robinandreeklund-collab/Strilas/docs/phase1-mounting.png

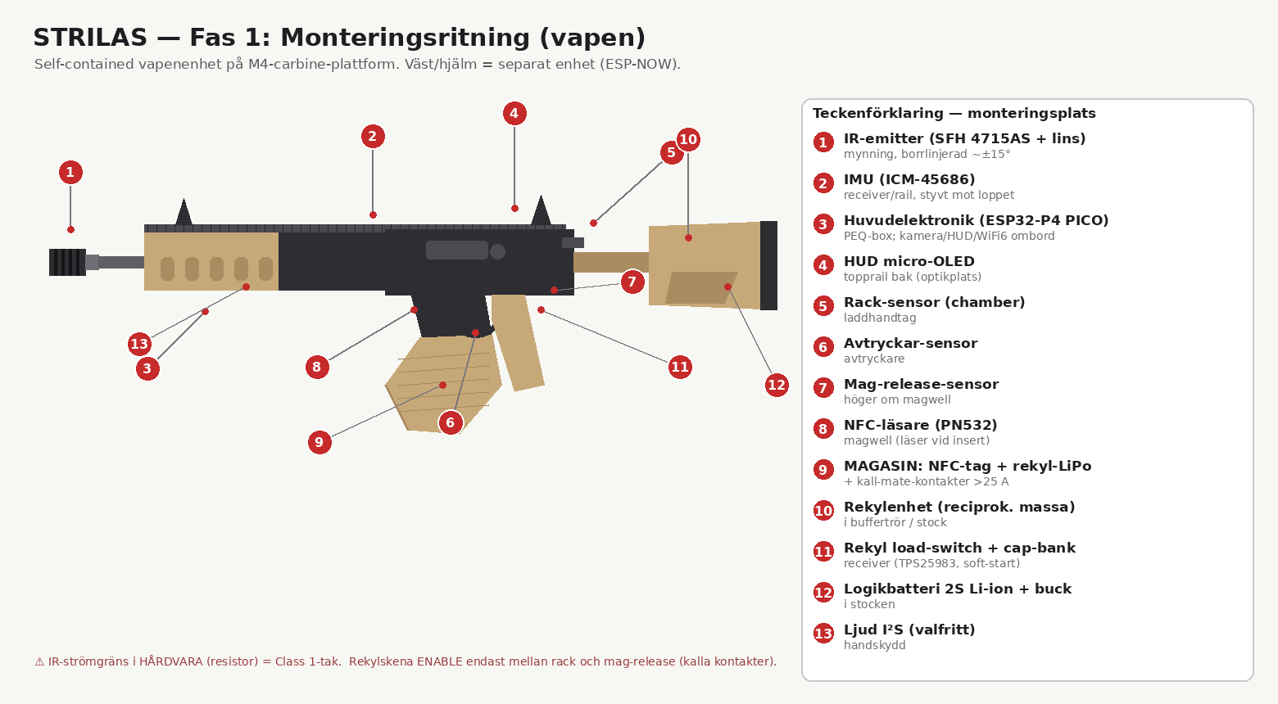
docs/phase1-mounting.png
