robinandreeklund-collab/Strilas/hardware/firecontrol-placement.png

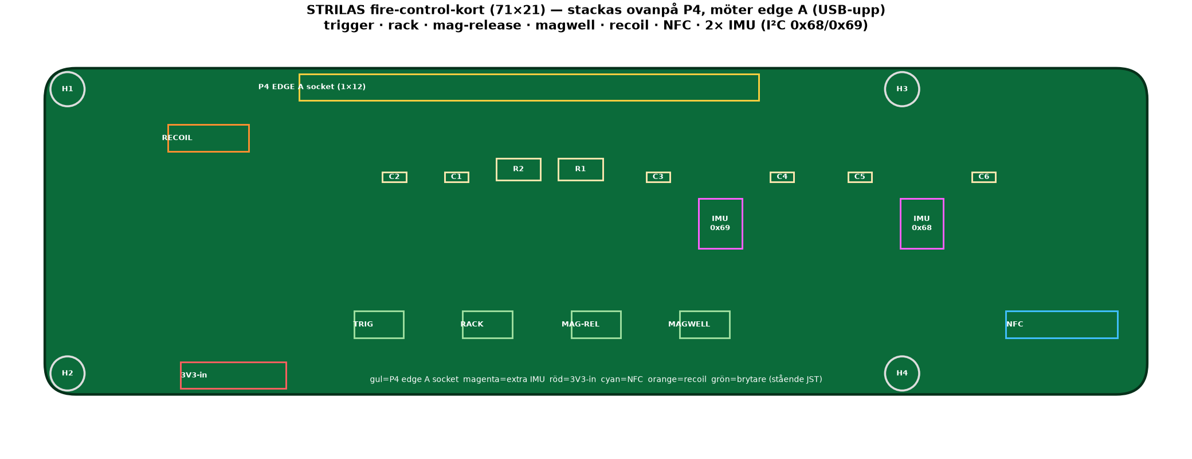
hardware/firecontrol-placement.png
