robinandreeklund-collab/Strilas/vapen-stack/ritningar/ballistik-avstand.png

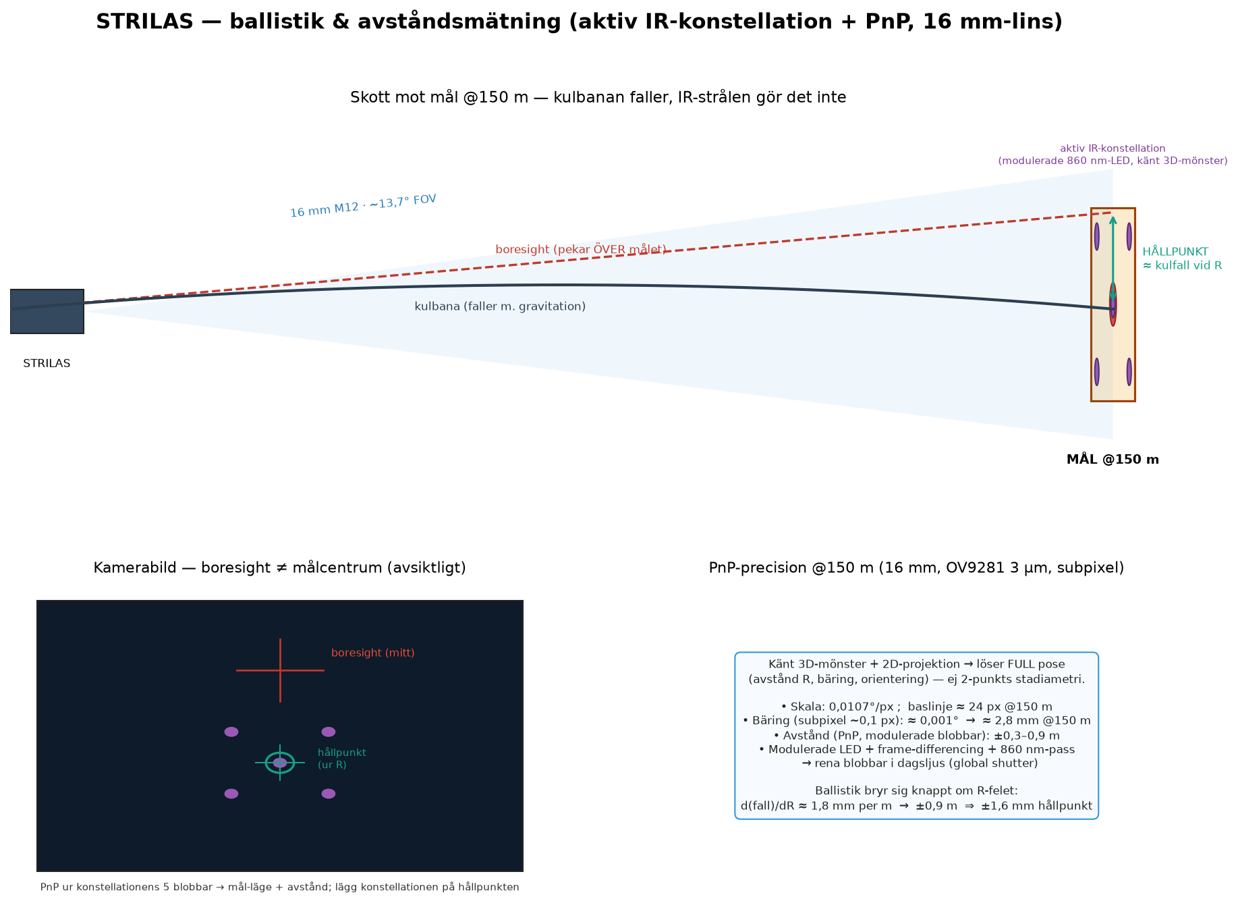
vapen-stack/ritningar/ballistik-avstand.png
