robinandreeklund-collab/Strilas/vapen-stack/ritningar/hitbox-simulering.png

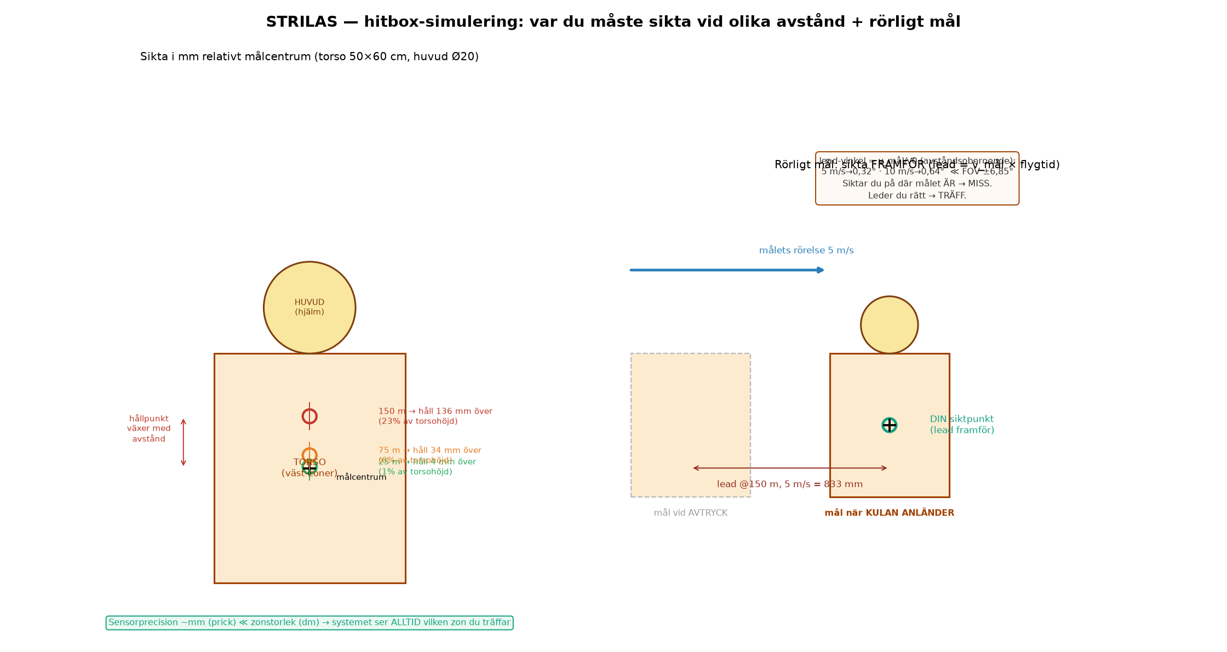
vapen-stack/ritningar/hitbox-simulering.png
