robinandreeklund-collab/Strilas/vapen-stack/ritningar/imu-breakout-koppling.png

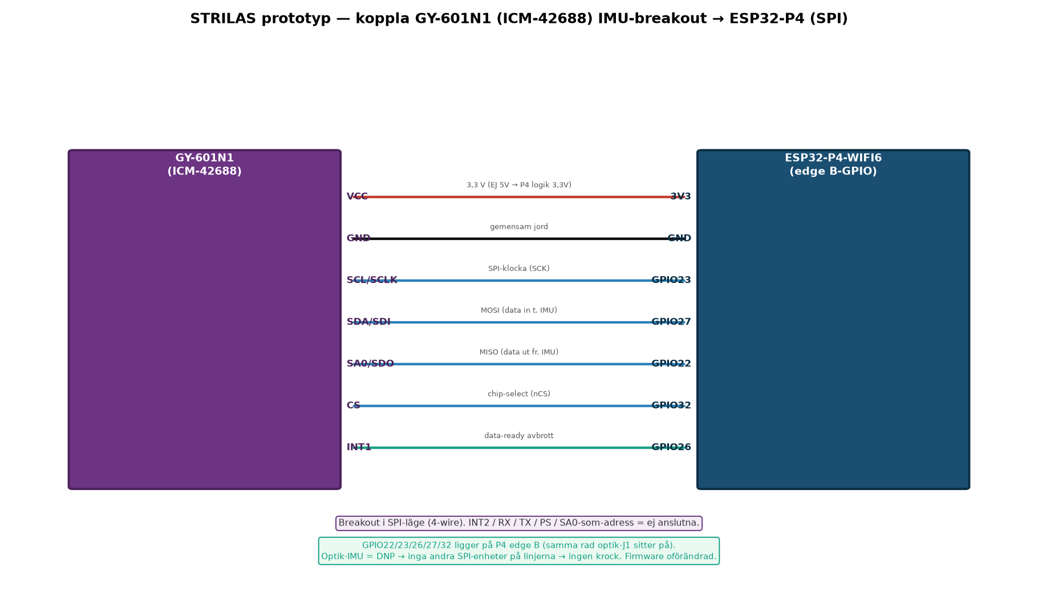
vapen-stack/ritningar/imu-breakout-koppling.png
