robinandreeklund-collab/Strilas/vapen-stack/ritningar/lead-rorligt-mal.png

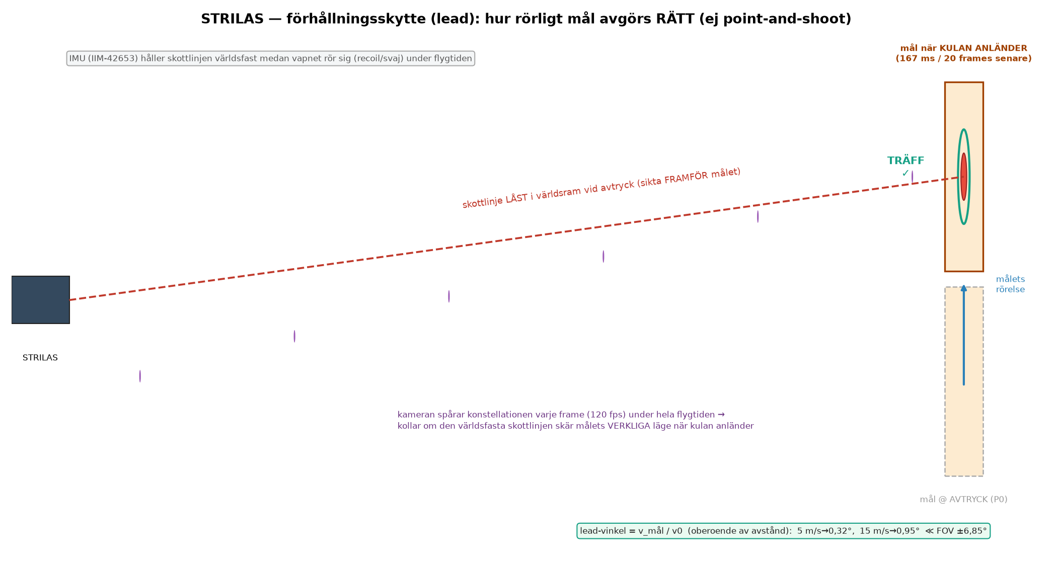
vapen-stack/ritningar/lead-rorligt-mal.png
