robinandreeklund-collab/Strilas/vapen-stack/ritningar/p4-pinmap-fysisk.png

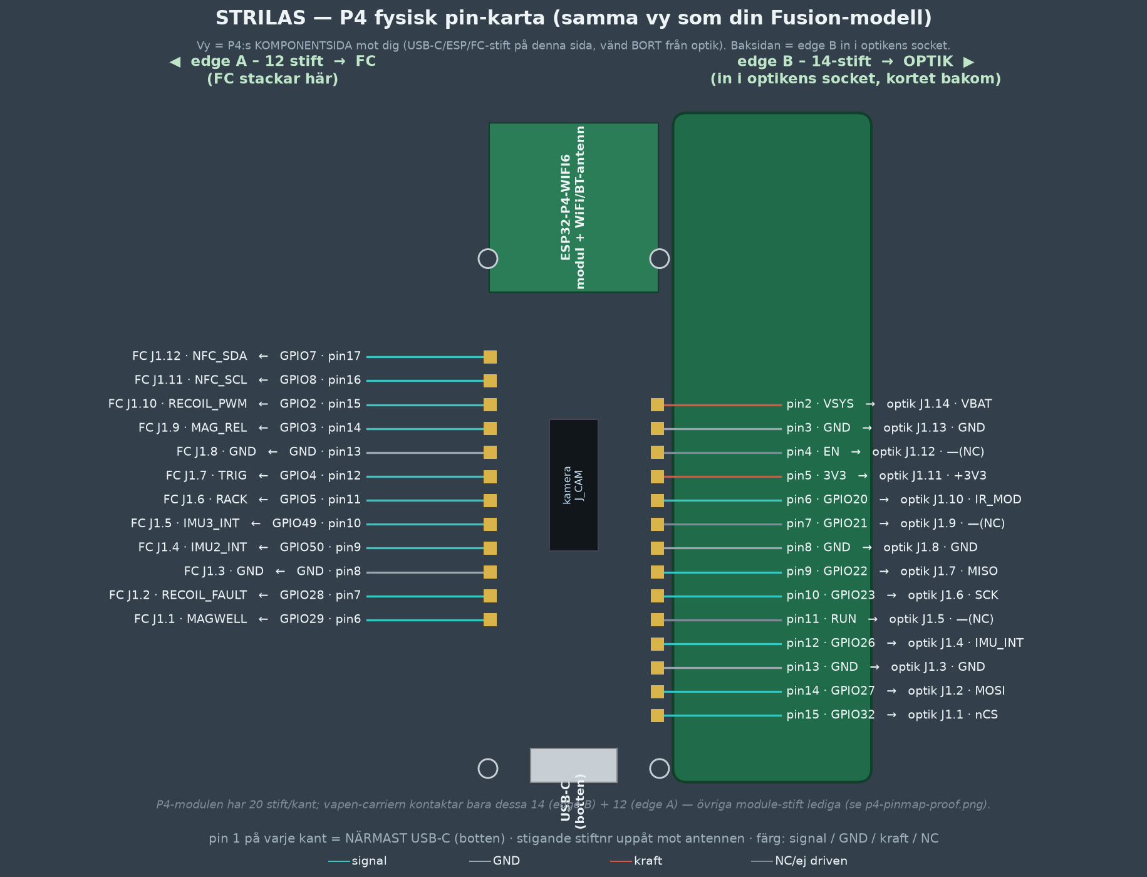
vapen-stack/ritningar/p4-pinmap-fysisk.png
