robinandreeklund-collab/Strilas/vapen-stack/ritningar/p4-pinmap-proof.png

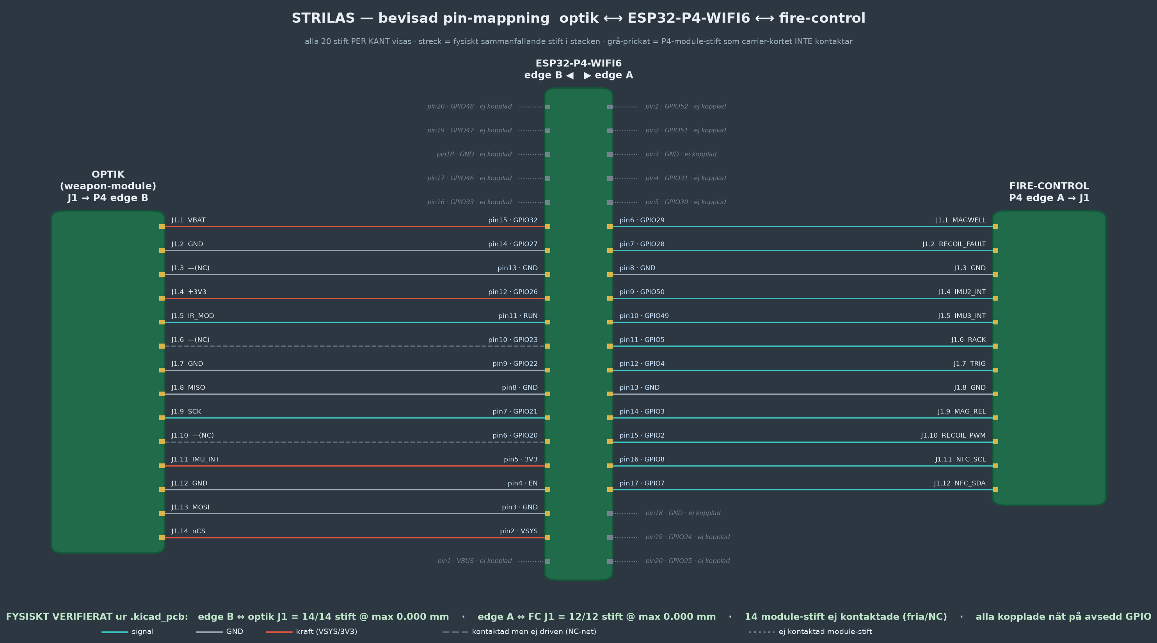
vapen-stack/ritningar/p4-pinmap-proof.png
