robinandreeklund-collab/Strilas/vapen-stack/ritningar/precision-felbudget.png

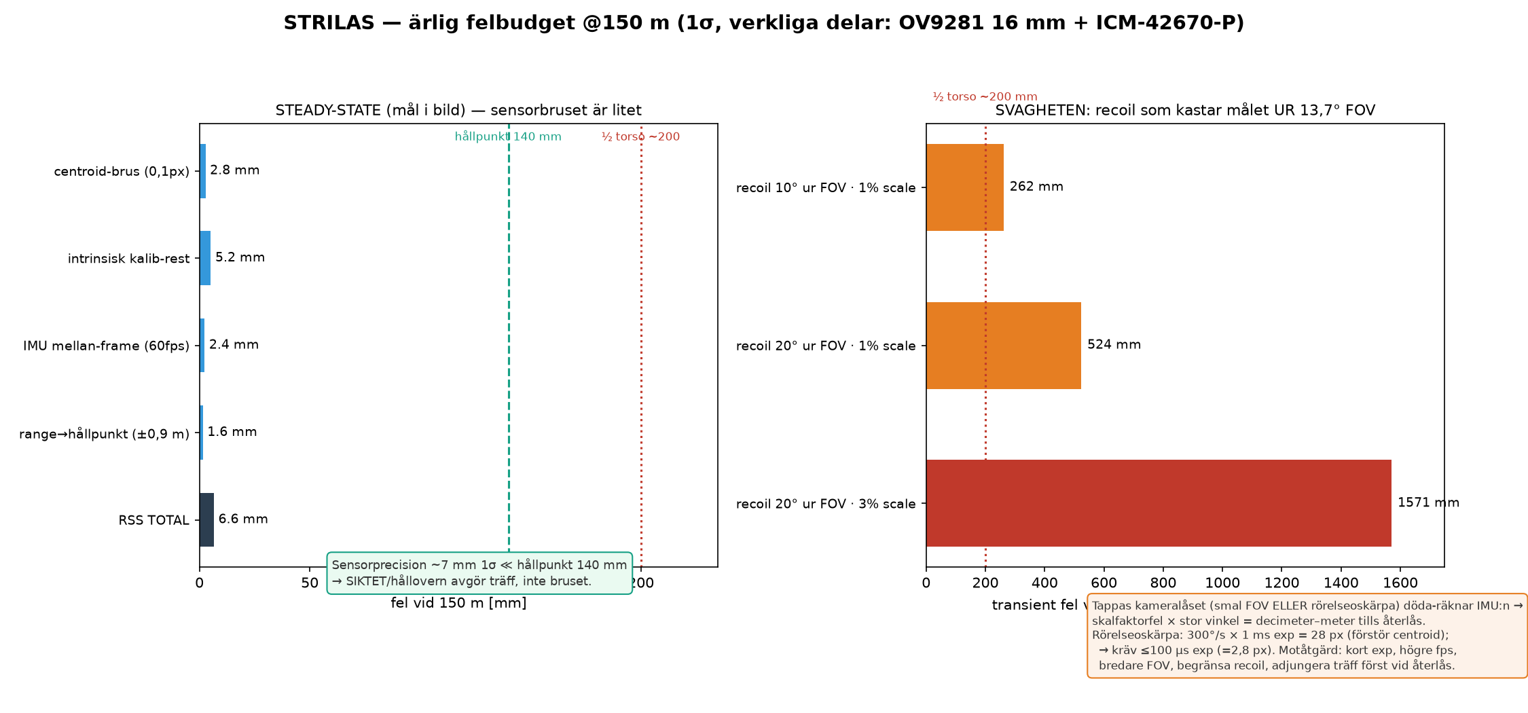
vapen-stack/ritningar/precision-felbudget.png
