robinandreeklund-collab/Strilas/vapen-stack/ritningar/precision-iim42653.png

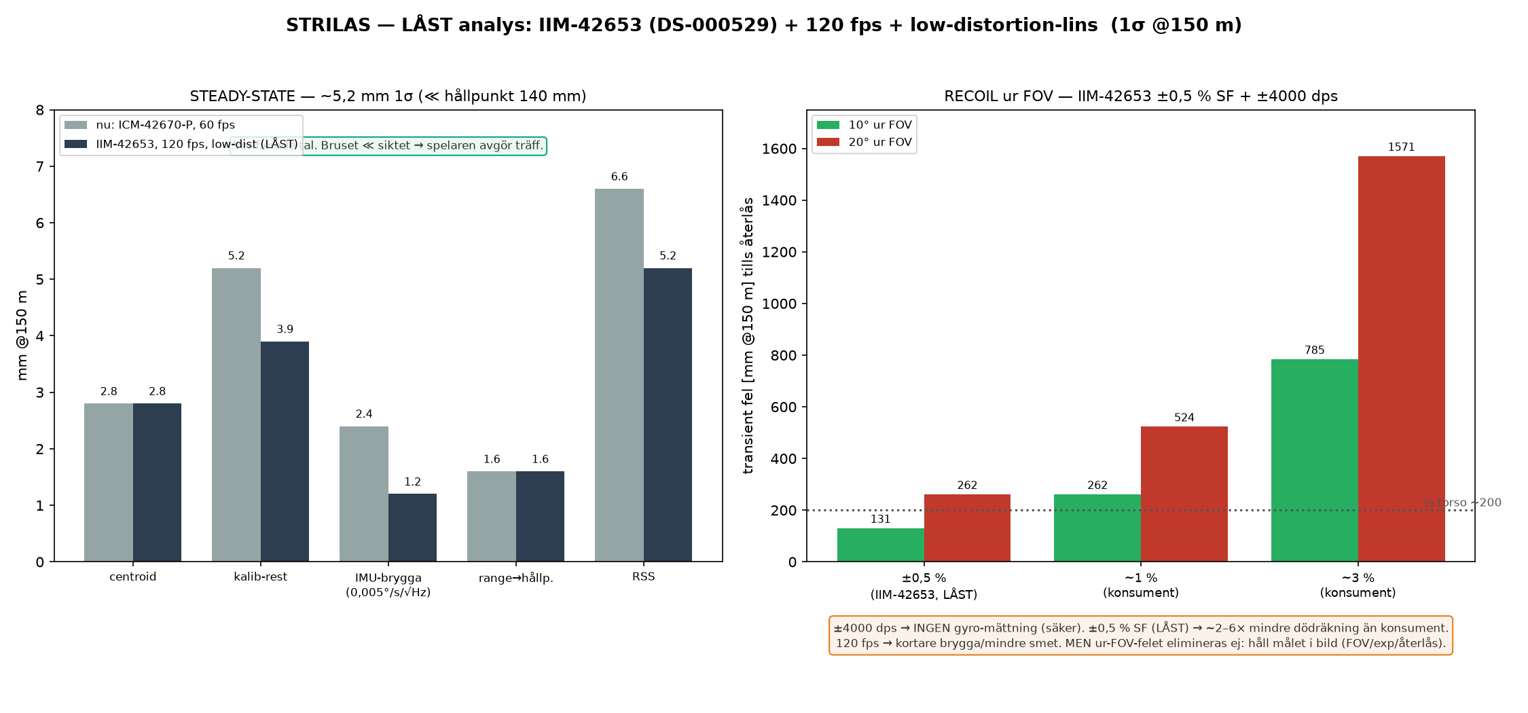
vapen-stack/ritningar/precision-iim42653.png
