robinandreeklund-collab/Strilas/vapen-stack/ritningar/skott-flode.png

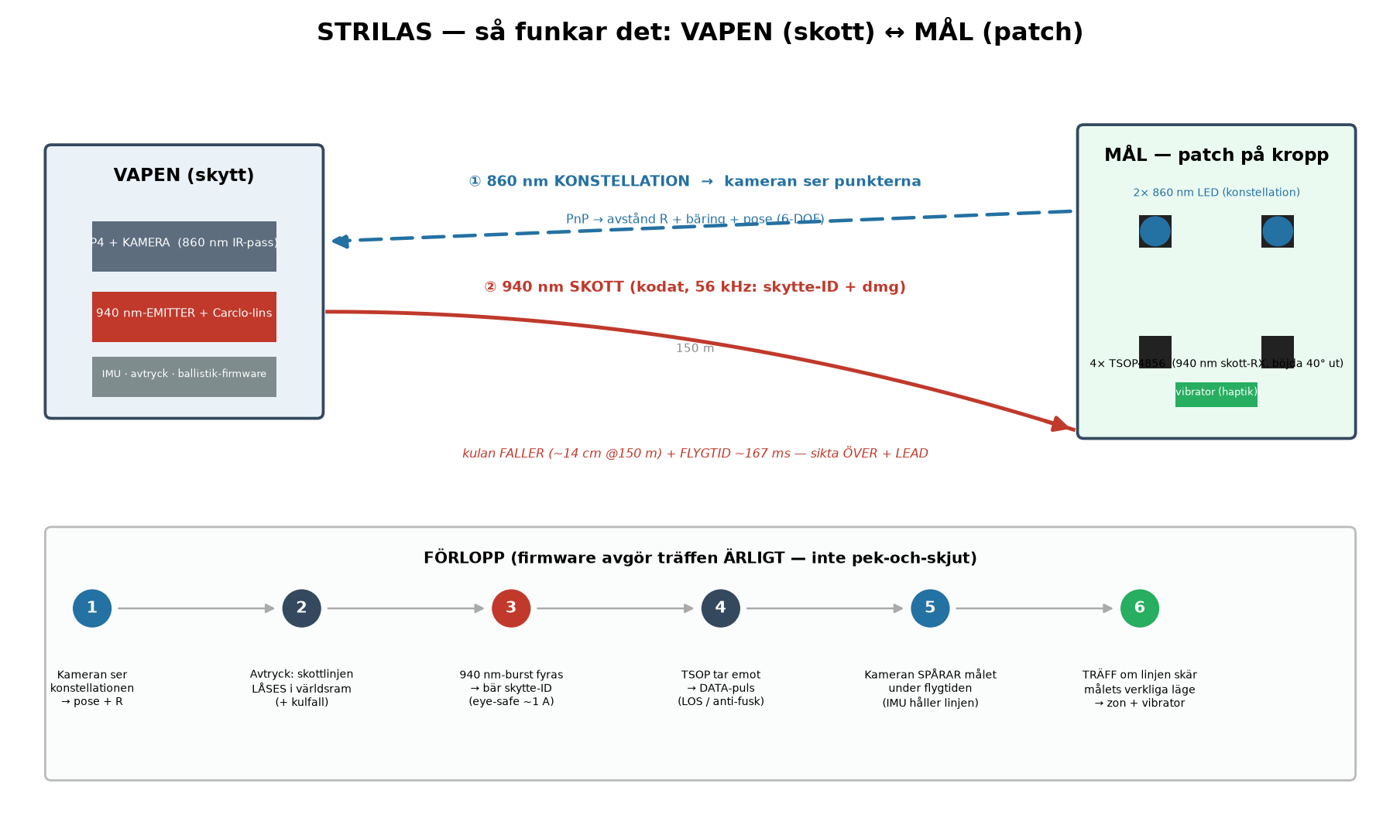
vapen-stack/ritningar/skott-flode.png
