robinandreeklund-collab/Strilas/vapen-stack/ritningar/spelare-topologi.png

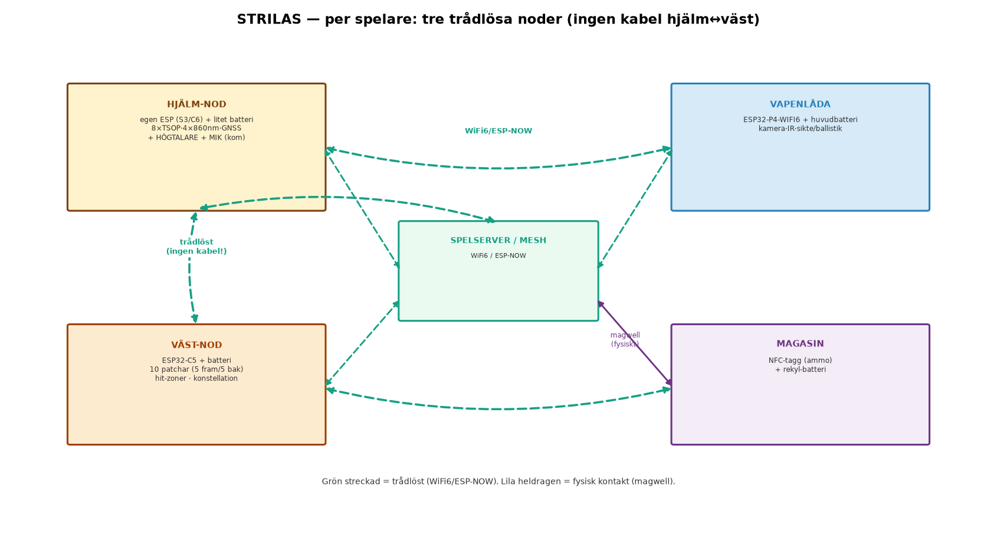
vapen-stack/ritningar/spelare-topologi.png
