robinandreeklund-collab/Strilas/vapen-stack/ritningar/system-helhet.png

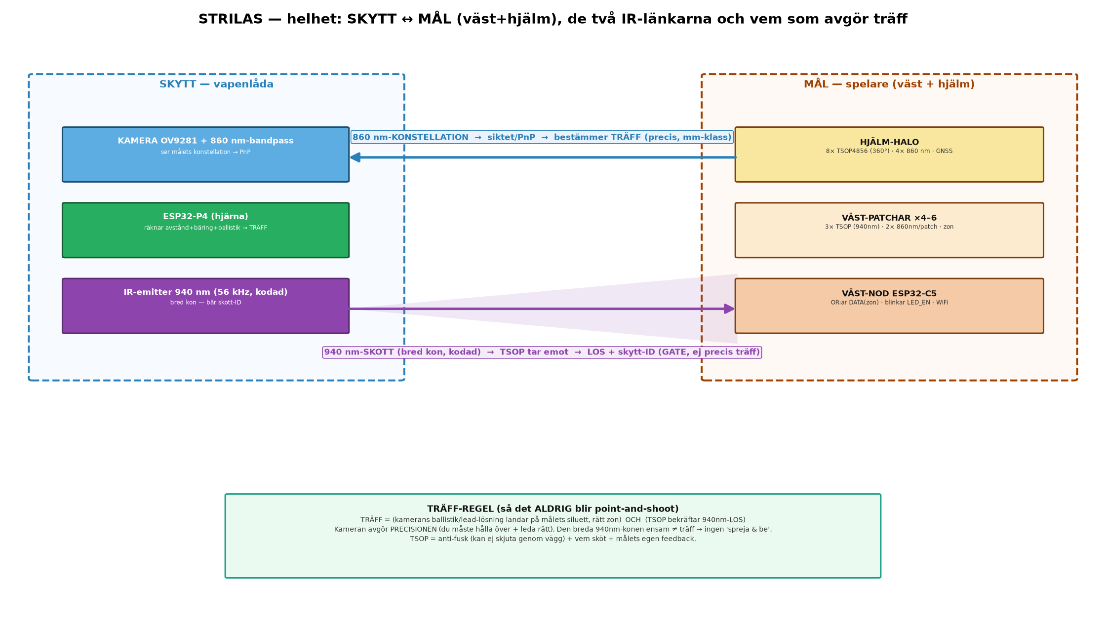
vapen-stack/ritningar/system-helhet.png
