robinandreeklund-collab/Strilas/vapen-stack/ritningar/system-oversikt.png

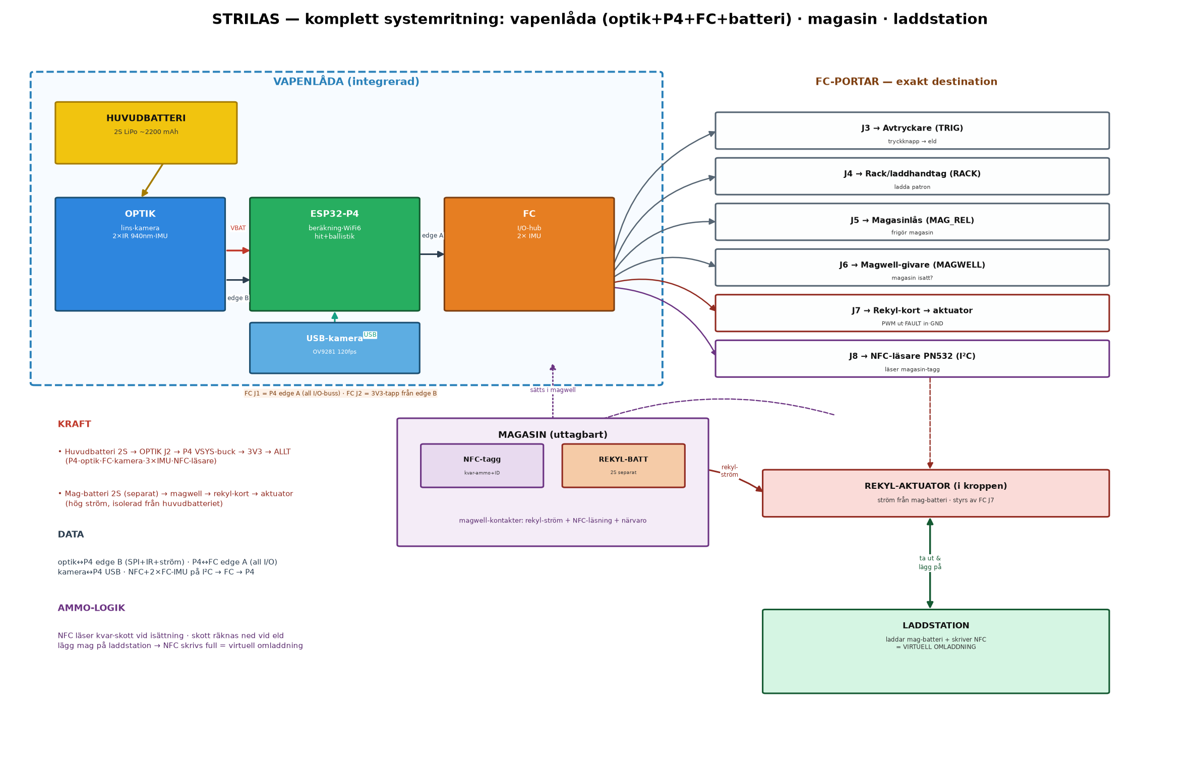
vapen-stack/ritningar/system-oversikt.png
