robinandreeklund-collab/Strilas/vapen-stack/ritningar/vapen-layout.png

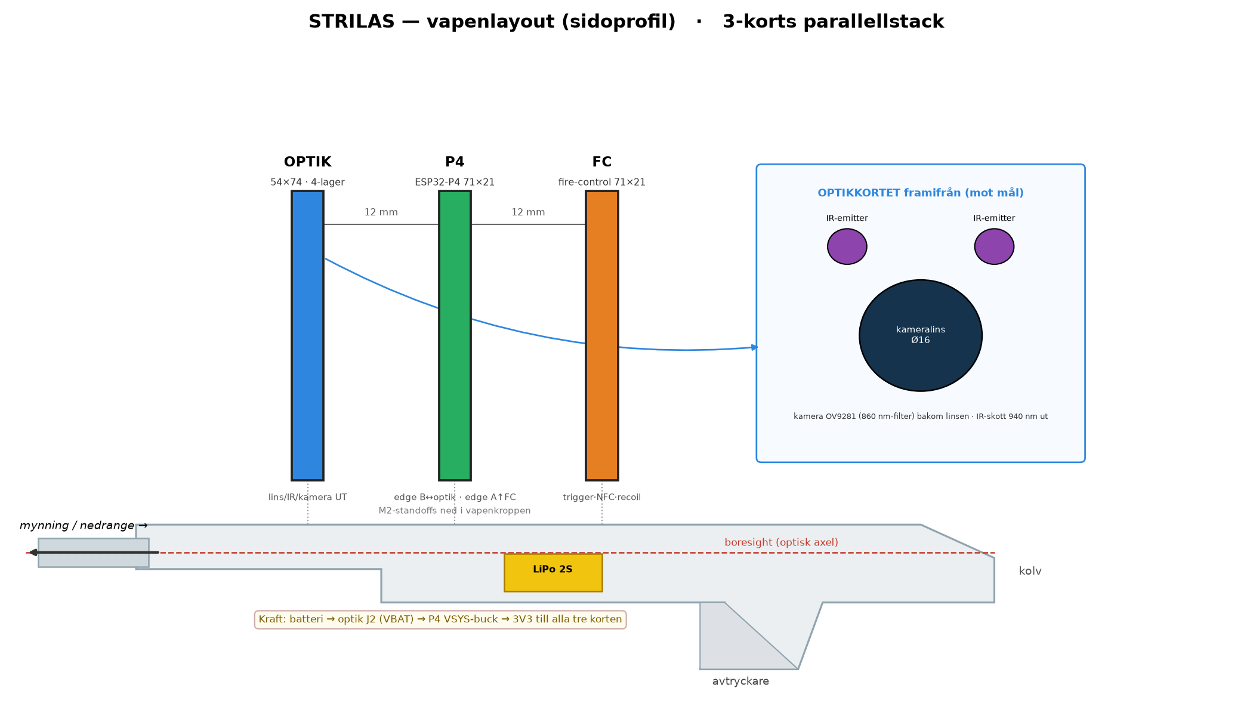
vapen-stack/ritningar/vapen-layout.png
