robinandreeklund-collab/Strilas/vapen-stack/ritningar/vest-haptik.png

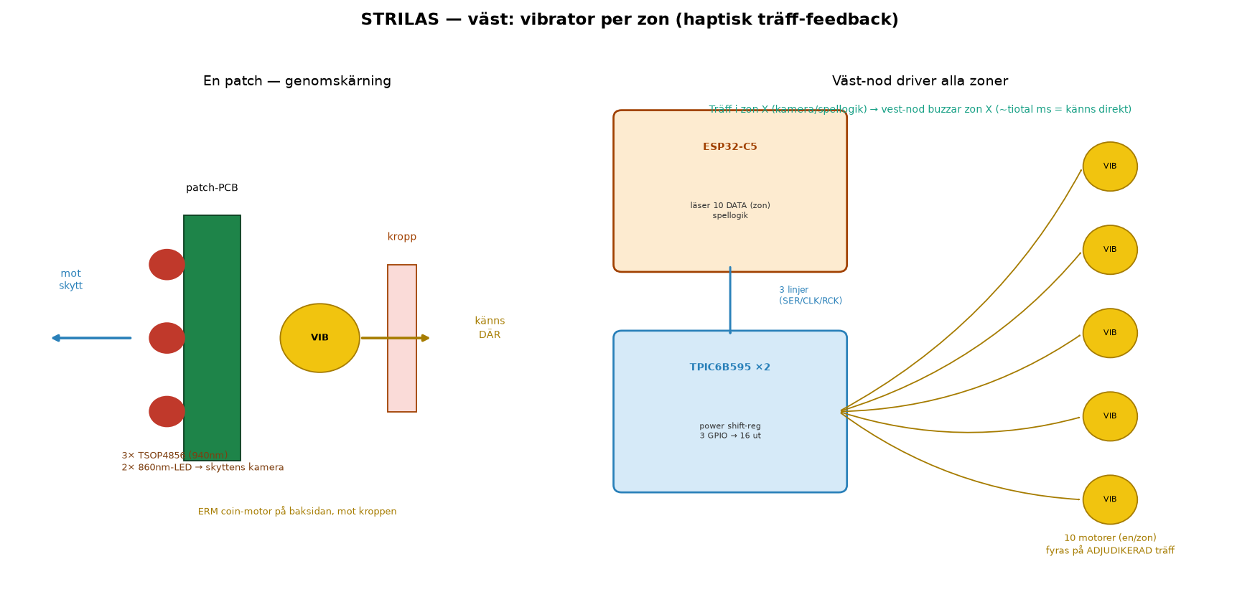
vapen-stack/ritningar/vest-haptik.png
