robinandreeklund-collab/Strilas/vapen-stack/ritningar/zonschema.png

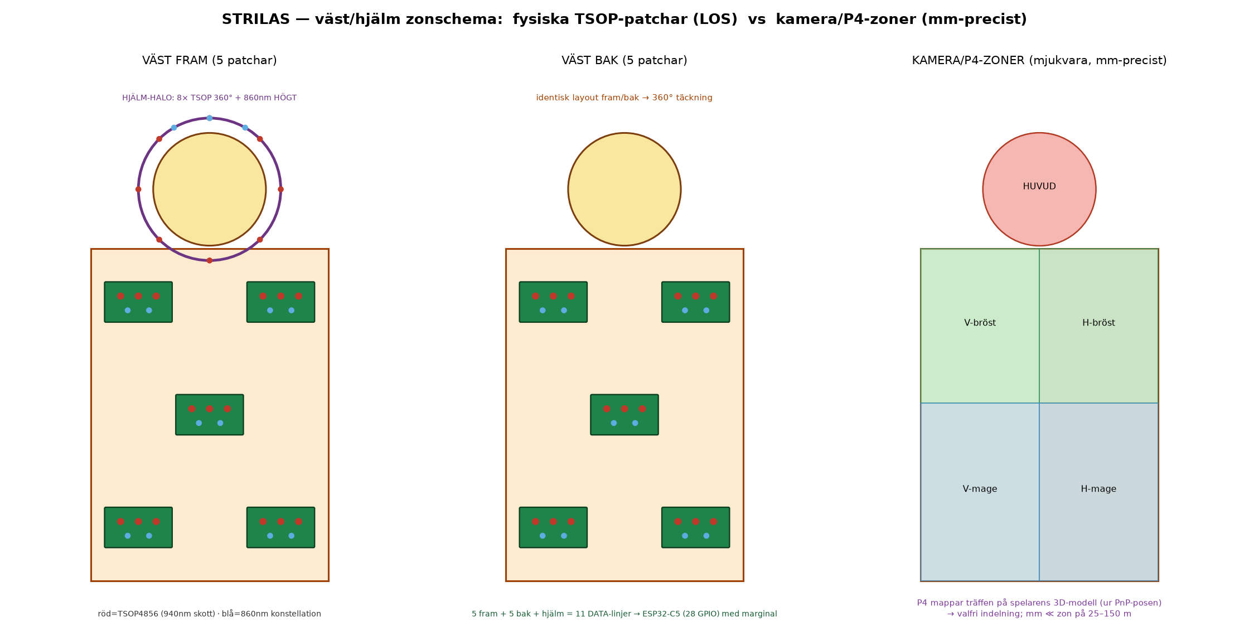
vapen-stack/ritningar/zonschema.png
