robinandreeklund-collab/Strilas/hardware/nextpcb/optik-bom.xls

Designator* | Quantity* | Manufacturer Part Number* | Manufacturer | Package/Footprint | Description | Procurement Type | Customer Note
R3 | 1 |  |  | R_0805_2012Metric | 0R1 DNP=1A/montera=3A | DNP | 3A-override (Rp): DNP = säker 1A fail-safe default; montera för 3A (medvetet labbeslut, kräver förnyad ögonsäkerhetsmätning)
R2 | 1 | WSL2512R2000FEA | Vishay | R_2512_6332Metric | Res 0.2R 1% 1W 2512 Kelvin-sense (lågt TCR) — CC-driver sätter ~1A (Vref/Rs) |  | Sourcebar 4-7 d (byt fr Yageo PE2512FKE070R200L som krävde manuell offert). Precisions-sense → bättre ström-/ögonsäkerhetsstabilitet. P=I²R≈0,2W ≪ 1W
R6 | 1 | RC0805FR-07100RL | Yageo | R_0805_2012Metric | Res 100R 1% 0805
R1,R7 | 2 | RC0805FR-07100KL | Yageo | R_0805_2012Metric | Res 100k 1% 1/8W 0805
C3,C4,C6 | 3 | GRM155R71H104KE14D | Murata | C_0402_1005Metric | MLCC 100nF 50V X7R 0402 — IN STOCK (byt fr Samsung CL05B104KO5NNNC: 4-20 d lead → kapat; samma 50V X7R-spec, billigare). Lager-koll cap-sampler
C8 | 1 | CL21B104KBCNNNC | Samsung | C_0805_2012Metric | MLCC 100nF 50V X7R 0805 — IN STOCK
C7 | 1 | CL21C101JBANNNC | Samsung | C_0805_2012Metric | MLCC 100pF 50V C0G 0805 — slingkomp
C2 | 1 | CL32A107MQVNNNE | Samsung | C_1210_3225Metric | MLCC 100uF 25V X5R 1210 (byt fr ej-matchad GRM32ER61E107ME20L) |  | verifiera vid manuell offert
C1 | 1 | CL31A106KBHNNNE | Samsung | C_1206_3216Metric | MLCC 10uF 25V X5R 1206 — IN STOCK
R4 | 1 | RC0805FR-0715KL | Yageo | R_0805_2012Metric | Res 15k 1% 0805 — CC-referensdelare (övre)
R5 | 1 | RC0805FR-071KL | Yageo | R_0805_2012Metric | Res 1k 1% 0805 — CC-referensdelare (undre)
C5 | 1 | CL05A105KP5NNNC | Samsung | C_0402_1005Metric | MLCC 1uF 10V X5R 0402 — IN STOCK
J2 | 1 | S2B-XH-A(LF)(SN) | JST | JST_XH_S2B-XH-A_1x02_P2.50mm_Horizontal | JST-XH 2-pol header 2.5mm THT | DNP | Kund handlöder själv (THT/ledad) — DNP: NextPCB monterar EJ, ej i centroid. Med i BOM som beställningsreferens.
R8 | 1 | RC0805FR-0747KL | Yageo | R_0805_2012Metric | Res 47k 1% 0805 — batteri-sense-delare (undre)
Q1 | 1 | AO3401A | Alpha & Omega | SOT-23 | P-MOSFET -30V SOT-23 (omvändpolaritets-skydd)
Q2 | 1 | AOD4184A | Alpha & Omega | TO-252-2 | N-MOSFET 40V logic-level DPAK (TO-252) — CC pass-FET (linjär)
U1 | 1 | ICM-42688-P | TDK InvenSense | InvenSense_LGA-14_2.5x3mm_ICM-456xx | 6-axlig hög-precisions-IMU LGA-14 2.5×3mm — ultralågt gyro-brus ~2.8 mdps/√Hz, ±2000dps/±16g; pin-kompatibel drop-in mot IIM-42653 |  | Vald för prototyp (i lager hos NextPCB, lägst brus → bäst INS-fusion)
U2 | 1 | OPA171AIDBVR | Texas Instruments | SOT-23-5 | Op-amp 36V 3MHz SOT-23-5 — CC-sänkans regulator
J1 | 1 | DS1023-1X14SF11 | Ckmtw | PinSocket_1x14_P2.54mm_Vertical | Stiftsockel 1x14 2.54mm THT (hona) — P4 edge B | DNP | Kund handlöder själv (THT/ledad) — DNP: NextPCB monterar EJ, ej i centroid. Med i BOM som beställningsreferens.
F1 | 1 | MF-MSMF300/16-2 | Bourns | Fuse_1812_4532Metric | PTC resättbar 3A-hold 16V 1812 — matningsskydd |  | OBS 2S 8,4V KRÄVER 16V-märkt (6V-varianter som miniSMDC300F duger EJ). In-stock 16V-variant utvärderas via sampler v2; MF-MSMF300/16 = orderbar referens
D2,D3 | 2 | SFH 4725AS | ams OSRAM | IR_Emitter_OSRAM_OSLON_Black_SFH4725S | IR-emitter 940nm OSLON Black SMD, bin 13 (aktiv drop-in för utgångna 4725S; samma paket C63062-A4141/footprint/optik) |  | NextPCB sourcar + SMT-placerar (precision UNDER LINSEN)
D1 | 1 | SMBJ12A | Littelfuse | D_SMB | TVS unidir 12V SMB
LENS1,LENS2 | 2 | 10195 | Carclo | Ø20 TIR-kollimator | IR-kollimatorlins (medium TIR ≤±7,5°) över varje emitter | DNP | Köps separat, monteras manuellt — ej PCB-monterad
LHOLD1,LHOLD2 | 2 | 10734 | Carclo | 20mm-hållare (ritn. 60575) | Lins-hållare (4 ben/lins) för Carclo 10195 över emittern | DNP | Köps separat, monteras manuellt — ej PCB-monterad
