robinandreeklund-collab/Strilas/hardware/nextpcb/vest-mb-bom.xls

Designator* | Quantity* | Manufacturer Part Number* | Manufacturer | Package/Footprint | Description | Procurement Type | Customer Note
R3,R4 | 2 | RC0805FR-07100KL | Yageo | R_0805_2012Metric | Res 100k 1% 1/8W 0805
C1,C5,C6,C7 | 4 | CL21B104KBCNNNC | Samsung | C_0805_2012Metric | MLCC 100nF 50V X7R 0805 — IN STOCK
C4 | 1 | CL32A107MQVNNNE | Samsung | C_1210_3225Metric | MLCC 100uF 25V X5R 1210 (byt fr ej-matchad GRM32ER61E107ME20L) |  | verifiera vid manuell offert
R2 | 1 | RC0805FR-0710KL | Yageo | R_0805_2012Metric | Res 10k 1% 0805
C2 | 1 | CL31A106KBHNNNE | Samsung | C_1206_3216Metric | MLCC 10uF 25V X5R 1206 — IN STOCK
C3 | 1 | CL31A226KAHNNNE | Samsung | C_1206_3216Metric | MLCC 22uF 25V X5R 1206 — buck-utgång
J13 | 1 | XT30PW-M | AMASS | AMASS_XT30PW-M_1x02_P2.50mm_Horizontal | XT30PW-M kraftkontakt genomplåt (2S-batteri in, ≥15A) — IN STOCK (kontakt-sampler) |  | MONTERAS av NextPCB (kontakt-test) — sourcas + THT-monteras, ej handlödd
R1 | 1 | RC0805FR-0731K6L | Yageo | R_0805_2012Metric | Res 31.6k 1% 0805 — buck FB (övre, 3.33V)
L1 | 1 | SWPA5040S4R7MT | Sunlord | L_Changjiang_FNR5040S | Effektinduktor 4.7uH 5x5mm (buck) — IN STOCK (byt fr Changjiang FNR5040320R47M som krävde manuell offert; samma FNR5040-footprint) |  | Isat≈2.8A > 2A buck-topp ✓ (verifierad mot AP63203)
R5 | 1 | RC0805FR-0747KL | Yageo | R_0805_2012Metric | Res 47k 1% 0805 — batteri-sense-delare (undre)
Q1 | 1 | AOD403 | Alpha & Omega | TO-252-2 | P-MOSFET -30V DPAK (TO-252) AOD403 ~8mΩ — omvändpol-skydd (gate→GND). IN-STOCK-verifierad drop-in för AOD4185A (ej i lager); -30V >> 2S 8,4V |  | samma A&O DPAK-pinout som AOD4185A → footprint oförändrad
U1 | 1 | AP63203WU-7 | Diodes Inc | TSOT-23-6 | Synk-buck 3.8-32Vin 2A TSOT23-6 — 2S→3V3 @1A
J12 | 1 | DS1023-1X20SF11 | Ckmtw | PinSocket_1x20_P2.54mm_Vertical | Stiftsockel 1x20 2.54mm THT (hona) — P4-WIFI6 edge A (signaler) |  | MONTERAS av NextPCB (kontakt-test) — sourcas + THT-monteras, ej handlödd
J11 | 1 | DS1023-1X20SF11 | Ckmtw | PinSocket_1x20_P2.54mm_Vertical | Stiftsockel 1x20 2.54mm THT (hona) — P4-WIFI6 edge B (kraft) |  | MONTERAS av NextPCB (kontakt-test) — sourcas + THT-monteras, ej handlödd
F1 | 1 | MF-MSMF300/16-2 | Bourns | Fuse_1812_4532Metric | PTC resättbar 3A-hold 16V 1812 — matningsskydd |  | OBS 2S 8,4V KRÄVER 16V-märkt (6V-varianter som miniSMDC300F duger EJ). In-stock 16V-variant utvärderas via sampler v2; MF-MSMF300/16 = orderbar referens
D1 | 1 | SMBJ12A | Littelfuse | D_SMB | TVS unidir 12V SMB
U2,U3 | 2 | TPIC6B595DWR | Texas Instruments | SOIC-20W_7.5x12.8mm_P1.27mm | Power 8-bit shift-register SOIC-20W, 150mA/kanal open-drain (vibrator-driver)
J1,J2,J3,J4,J5,J6,J7,J8,J9,J10 | 10 | S6B-PH-K-S(LF)(SN) | JST | JST_PH_S6B-PH-K_1x06_P2.00mm_Horizontal | JST-PH 6-pol header 2.0mm THT SIDOMONTERAD (S-typ, låg bygghöjd) → väst-patch (pin1-5) + zon-vibrator (pin6) |  | MONTERAS av NextPCB (kontakt-test) — sourcas + THT-monteras, ej handlödd
