robinandreeklund-collab/Strilas/leverans/common-sampler/common-sampler-bom.xls

Designator* | Quantity* | Manufacturer Part Number* | Manufacturer | Package/Footprint | Description | Procurement Type | Customer Note
R1 | 1 | RC0805FR-0710KL | Yageo | 10k 0805 | Res 10k 1% 0805 ★gemensam |  | Gemensam-komponent (lager-koll)
R2 | 1 | RC0805FR-074K7L | Yageo | 4k7 0805 | Res 4.7k 1% 0805 (I2C-pullup) |  | Gemensam-komponent (lager-koll)
R3 | 1 | RC0805FR-07100RL | Yageo | 100R 0805 | Res 100R 1% 0805 |  | Gemensam-komponent (lager-koll)
R4 | 1 | RC0805FR-07220RL | Yageo | 220R 0805 | Res 220R 1% 0805 (gate) |  | Gemensam-komponent (lager-koll)
R5 | 1 | RC0805FR-071KL | Yageo | 1k 0805 | Res 1k 1% 0805 |  | Gemensam-komponent (lager-koll)
R6 | 1 | RC0805FR-072K2L | Yageo | 2.2k 0805 | Res 2.2k 1% 0805 (mik-bias) |  | Gemensam-komponent (lager-koll)
R7 | 1 | RC0805FR-0715KL | Yageo | 15k 0805 | Res 15k 1% 0805 (CC-delare) |  | Gemensam-komponent (lager-koll)
R8 | 1 | RC0805FR-0731K6L | Yageo | 31.6k 0805 | Res 31.6k 1% 0805 (buck-FB) |  | Gemensam-komponent (lager-koll)
R9 | 1 | RC0805FR-07100KL | Yageo | 100k 0805 | Res 100k 1% 0805 |  | Gemensam-komponent (lager-koll)
R10 | 1 | CRCW251210R0FKEGHP | Vishay | 10R 2512 | Res 10R 1% 2W 2512 (LED-serie, EFFEKT) |  | Gemensam-komponent (lager-koll)
R11 | 1 | PE2512FKE070R200L | Yageo | 0R2 2512 | Res 0.2R 1% 2W 2512 (CC-sense) |  | Gemensam-komponent (lager-koll)
C1 | 1 | CL05B104KO5NNNC | Samsung | 100nF 0402 | MLCC 100nF 50V X7R 0402 ★ (vs 0805 -> VÄLJ ETT) |  | Gemensam-komponent (lager-koll)
C2 | 1 | CL21B104KBCNNNC | Samsung | 100nF 0805 | MLCC 100nF 50V X7R 0805 ★ (vs 0402 -> VÄLJ ETT) |  | Gemensam-komponent (lager-koll)
C3 | 1 | CL05A105KP5NNNC | Samsung | 1uF 0402 | MLCC 1uF 10V X5R 0402 (vs 0805 -> VÄLJ ETT) |  | Gemensam-komponent (lager-koll)
C4 | 1 | GRM21BR61E105KA99L | Murata | 1uF 0805 | MLCC 1uF 25V X5R 0805 (high-runner, in-stock-alt) |  | Gemensam-komponent (lager-koll)
C5 | 1 | CL21C101JBANNNC | Samsung | 100pF 0805 | MLCC 100pF 50V C0G 0805 (slingkomp) |  | Gemensam-komponent (lager-koll)
C6 | 1 | CL31A106KBHNNNE | Samsung | 10uF 1206 | MLCC 10uF 25V X5R 1206 ★gemensam |  | Gemensam-komponent (lager-koll)
C7 | 1 | CL31A226KAHNNNE | Samsung | 22uF 1206 | MLCC 22uF 25V X5R 1206 (buck-ut) |  | Gemensam-komponent (lager-koll)
C8 | 1 | CL32A107MQVNNNE | Samsung | 100uF 1210 | MLCC 100uF 25V X5R 1210 (bulk, in-stock-alt) |  | Gemensam-komponent (lager-koll)
D1 | 1 | BAT54-7-F | Diodes | BAT54 SOD-123 | Schottky (diod-OR TSOP) |  | Gemensam-komponent (lager-koll)
D2 | 1 | SMBJ12A | Littelfuse | SMBJ12A SMB | TVS 12V (matningsskydd) |  | Gemensam-komponent (lager-koll)
Q1 | 1 | AO3400A | AOS | AO3400 SOT-23 | N-FET 30V (LED-driver) |  | Gemensam-komponent (lager-koll)
Q2 | 1 | AO3401A | AOS | AO3401 SOT-23 | P-FET -30V (rev-skydd) |  | Gemensam-komponent (lager-koll)
Q3 | 1 | AOD4184A | AOS | AOD4184A TO-252 | N-FET DPAK (CC pass) |  | Gemensam-komponent (lager-koll)
L1 | 1 | FNR5040320R47M | Changjiang | 4.7uH FNR5040 | Induktor 4.7uH (buck) |  | Gemensam-komponent (lager-koll)
U1 | 1 | AP63203WU-7 | Diodes | AP63203 TSOT23-6 | Buck 2A (2S->3V3) |  | Gemensam-komponent (lager-koll)
U2 | 1 | HT7333-A | Holtek | HT7333 SOT-89 | LDO 3.3V 250mA (patch) |  | Gemensam-komponent (lager-koll)
U3 | 1 | OPA171AIDBVR | TI | OPA171 SOT23-5 | Op-amp (CC-regulator) |  | Gemensam-komponent (lager-koll)
