robinandreeklund-collab/Strilas/leverans/imu-sampler/imu-sampler-bom.xls

Designator* | Quantity* | Manufacturer Part Number* | Manufacturer | Package/Footprint | Description | Procurement Type | Customer Note
U1 | 1 | IIM-42653 | TDK InvenSense | InvenSense_LGA-14_2.5x3mm_ICM-456xx | BASLINJE: 6-ax industri, ±32g/±4000dps, -40..+105C |  | IMU-kandidat (lager-koll). Footprint korrekt paket; familj pin-kompatibel.
U2 | 1 | IIM-42652 | TDK InvenSense | InvenSense_LGA-14_2.5x3mm_ICM-456xx | 6-ax industri, ±16g/±2000dps, -40..+105C |  | IMU-kandidat (lager-koll). Footprint korrekt paket; familj pin-kompatibel.
U3 | 1 | ICM-42688-P | TDK InvenSense | InvenSense_LGA-14_2.5x3mm_ICM-456xx | 6-ax ultra-lagt brus (bast-i-klass gyro-brus) - precision |  | IMU-kandidat (lager-koll). Footprint korrekt paket; familj pin-kompatibel.
U4 | 1 | ICM-42670-P | TDK InvenSense | InvenSense_LGA-14_2.5x3mm_ICM-456xx | 6-ax lag-effekt (datablad i repo) |  | IMU-kandidat (lager-koll). Footprint korrekt paket; familj pin-kompatibel.
U5 | 1 | ICM-40609-D | TDK InvenSense | InvenSense_LGA-14_2.5x3mm_ICM-456xx | 6-ax hog-g ±32g |  | IMU-kandidat (lager-koll). Footprint korrekt paket; familj pin-kompatibel.
U6 | 1 | ICM-45686 | TDK InvenSense | InvenSense_LGA-14_2.5x3mm_ICM-456xx | Ny-gen 6-ax, ±32g/±4000dps, lagre brus an 426xx |  | IMU-kandidat (lager-koll). Footprint korrekt paket; familj pin-kompatibel.
U7 | 1 | ICM-42688-V | TDK InvenSense | InvenSense_LGA-14_2.5x3mm_ICM-456xx | ICM-42688 V-variant (brett lager) |  | IMU-kandidat (lager-koll). Footprint korrekt paket; familj pin-kompatibel.
U8 | 1 | BMI270 | Bosch | Bosch_LGA-14_3x2.5mm_P0.5mm | 6-ax lag-effekt (drone/wearable), brett lager |  | IMU-kandidat (lager-koll). Footprint korrekt paket; familj pin-kompatibel.
U9 | 1 | BMI323 | Bosch | Bosch_LGA-14_3x2.5mm_P0.5mm | 6-ax ny-gen Bosch |  | IMU-kandidat (lager-koll). Footprint korrekt paket; familj pin-kompatibel.
U10 | 1 | BMI160 | Bosch | Bosch_LGA-14_3x2.5mm_P0.5mm | 6-ax (legacy men brett lager) |  | IMU-kandidat (lager-koll). Footprint korrekt paket; familj pin-kompatibel.
U11 | 1 | BMI088 | Bosch | LGA-16_3x3mm_P0.5mm | 6-ax HOG-VIBRATION (drone/robot) - bra for vapen-rekyl. OBS LGA-16 4.5mm (footprint approx) |  | IMU-kandidat (lager-koll). Footprint korrekt paket; familj pin-kompatibel.
U12 | 1 | LSM6DSR | STMicro | LGA-14_3x2.5mm_P0.5mm_LayoutBorder3x4y | 6-ax ±4000dps (matchar IIM-42653 dps) |  | IMU-kandidat (lager-koll). Footprint korrekt paket; familj pin-kompatibel.
U13 | 1 | LSM6DSO32 | STMicro | LGA-14_3x2.5mm_P0.5mm_LayoutBorder3x4y | 6-ax ±32g/±2000dps lag-effekt |  | IMU-kandidat (lager-koll). Footprint korrekt paket; familj pin-kompatibel.
U14 | 1 | LSM6DSV16X | STMicro | LGA-14_3x2.5mm_P0.5mm_LayoutBorder3x4y | 6-ax ±4000dps + inbyggd sensor-fusion (MLC) |  | IMU-kandidat (lager-koll). Footprint korrekt paket; familj pin-kompatibel.
U15 | 1 | ISM330DHCX | STMicro | LGA-14_3x2.5mm_P0.5mm_LayoutBorder3x4y | 6-ax industri ±4000dps (maskin/robot) |  | IMU-kandidat (lager-koll). Footprint korrekt paket; familj pin-kompatibel.
U16 | 1 | ASM330LHHX | STMicro | LGA-14_3x2.5mm_P0.5mm_LayoutBorder3x4y | 6-ax fordon AEC-Q100, ±4000dps (robustast) |  | IMU-kandidat (lager-koll). Footprint korrekt paket; familj pin-kompatibel.
U17 | 1 | ICM-20948 | TDK InvenSense | InvenSense_QFN-24_3x3mm_P0.4mm | 9-AXEL accel+gyro+magnetometer - bäring utan GNSS |  | IMU-kandidat (lager-koll). Footprint korrekt paket; familj pin-kompatibel.
U18 | 1 | MPU-9250 | TDK InvenSense | InvenSense_QFN-24_3x3mm_P0.4mm | 9-AXEL legacy men brett lager (EOL - verifiera) |  | IMU-kandidat (lager-koll). Footprint korrekt paket; familj pin-kompatibel.
