robinandreeklund-collab/Strilas/vapen-stack/nextpcb/vest-patch-bom.xls

Designator* | Quantity* | Manufacturer Part Number* | Manufacturer | Package/Footprint | Description | Procurement Type | Customer Note
C2,C3,C4,C5 | 4 | CL05B104KO5NNNC | Samsung | C_0805_2012Metric | MLCC 100nF 50V X7R
R3,R4,R5 | 3 | CRCW251210R0FKEGHP | Vishay | R_2512_6332Metric | Res 10R 1% 2W 2512 (HP) — LED-serieR konstellation |  | OBS max ~50% duty (2,5W topp @0,5A)
R1 | 1 | RC0805FR-0710KL | Yageo | R_0805_2012Metric | Res 10k 1% 0805
C1 | 1 | CL31A106KBHNNNE | Samsung | C_1206_3216Metric | MLCC 10uF 25V X5R 1206
R2 | 1 | RC0805FR-07220RL | Yageo | R_0805_2012Metric | Res 220R 1% 1/8W 0805
Q1 | 1 | AO3400A | Alpha & Omega | SOT-23 | N-MOSFET 30V SOT-23 (väst LED-driver 56kHz)
D1,D2,D3,D4 | 4 | BAT54-7-F | Diodes Inc | D_SOD-123 | Schottky SOD-123 (OR av TSOP-utgångar)
D7,D8,D9,D10 | 4 |  |  | PinHeader_1x02_P2.54mm_Vertical | LED-tab (OSLON-micro-PCB, ben böjs 40° UT som TSOP) | DNP | Kund sourcar + lödder själv (TH-kontakt)
D5,D6 | 2 | SFH 4715AS | ams OSRAM | IR_Emitter_OSRAM_OSLON_Black_SFH4725S | IR-LED 860 nm OSLON Black SMD, Ie 780 mW/sr@1A (konstellation) | C | NextPCB SMT-PLACERAR (precision); kund levererar LED:n. Matcha kamerans 860 nm IR-pass
U1,U2,U3,U4 | 4 | TSOP4856 | Vishay | Vishay_MOLD-3Pin | IR-mottagare 56 kHz (940 nm), LEDAD MOLD-3 (genomplåt/THT) | DNP | Kund sourcar + lödder själv (TH-kontakt)
J1 | 1 | 2.54-1x05 | generisk | PinHeader_1x05_P2.54mm_Vertical | Stiftlist 1x05 2.54 mm → väst-moderkortets zon-kontakt | DNP | Kund sourcar + lödder själv (TH-kontakt)
