robinandreeklund-collab/Strilas/leverans/socket-sampler/socket-sampler-bom.xls

Designator* | Quantity* | Manufacturer Part Number* | Manufacturer | Package/Footprint | Description | Procurement Type | Customer Note
J1 | 1 | DS1023-1x3SF11 | Ckmtw | PinSocket_1x03_P2.54mm_Vertical | Hona 1x3 2.54 THT — kraft-tapp (kinesisk basic-lib) |  | LAGER-KOLL: vilket marke ar In Stock + kan THT-monteras (kortet bestalls EJ)
J2 | 1 | PPTC031LFBN-RC | Sullins | PinSocket_1x03_P2.54mm_Vertical | Hona 1x3 2.54 THT — kraft-tapp (kontroll: Sullins var Pending) |  | LAGER-KOLL: vilket marke ar In Stock + kan THT-monteras (kortet bestalls EJ)
J3 | 1 | DS1023-1x7SF11 | Ckmtw | PinSocket_1x07_P2.54mm_Vertical | Hona 1x7 2.54 THT — XIAO/breakout |  | LAGER-KOLL: vilket marke ar In Stock + kan THT-monteras (kortet bestalls EJ)
J4 | 1 | PPTC071LFBN-RC | Sullins | PinSocket_1x07_P2.54mm_Vertical | Hona 1x7 2.54 THT — XIAO/breakout (kontroll) |  | LAGER-KOLL: vilket marke ar In Stock + kan THT-monteras (kortet bestalls EJ)
J5 | 1 | DS1023-1x14SF11 | Ckmtw | PinSocket_1x14_P2.54mm_Vertical | Hona 1x14 2.54 THT — P4 edge A (optik) |  | LAGER-KOLL: vilket marke ar In Stock + kan THT-monteras (kortet bestalls EJ)
J6 | 1 | PPTC141LFBN-RC | Sullins | PinSocket_1x14_P2.54mm_Vertical | Hona 1x14 2.54 THT — P4 edge A (kontroll) |  | LAGER-KOLL: vilket marke ar In Stock + kan THT-monteras (kortet bestalls EJ)
J7 | 1 | DS1023-1x15SF11 | Ckmtw | PinSocket_1x15_P2.54mm_Vertical | Hona 1x15 2.54 THT — P4 edge (firecontrol) |  | LAGER-KOLL: vilket marke ar In Stock + kan THT-monteras (kortet bestalls EJ)
J8 | 1 | PPTC151LFBN-RC | Sullins | PinSocket_1x15_P2.54mm_Vertical | Hona 1x15 2.54 THT — P4 edge (kontroll) |  | LAGER-KOLL: vilket marke ar In Stock + kan THT-monteras (kortet bestalls EJ)
J9 | 1 | DS1023-1x20SF11 | Ckmtw | PinSocket_1x20_P2.54mm_Vertical | Hona 1x20 2.54 THT — P4-WIFI6 edge A/B (helmet/vest-mb, 4 st) |  | LAGER-KOLL: vilket marke ar In Stock + kan THT-monteras (kortet bestalls EJ)
J10 | 1 | PPTC201LFBN-RC | Sullins | PinSocket_1x20_P2.54mm_Vertical | Hona 1x20 2.54 THT — P4-WIFI6 edge (kontroll) |  | LAGER-KOLL: vilket marke ar In Stock + kan THT-monteras (kortet bestalls EJ)
J11 | 1 | SSW-120-01-T-S | Samtec | PinSocket_1x20_P2.54mm_Vertical | Hona 1x20 2.54 THT — P4-WIFI6 edge (premium-referens) |  | LAGER-KOLL: vilket marke ar In Stock + kan THT-monteras (kortet bestalls EJ)
