robinandreeklund-collab/Strilas/leverans/kontakt-sampler/kontakt-sampler-bom.xls

Designator* | Quantity* | Manufacturer Part Number* | Manufacturer | Package/Footprint | Description | Procurement Type | Customer Note
J1 | 1 | PPTC031LFBN-RC | Sullins | PinSocket_1x03_P2.54mm_Vertical | Hona 1x3 2.54 THT — kraft-tapp 3V3/GND |  | MONTERAS av NextPCB (kontakt-monteringstest) — bekrafta In Stock + att THT-montering gar
J2 | 1 | PPTC071LFBN-RC | Sullins | PinSocket_1x07_P2.54mm_Vertical | Hona 1x7 2.54 THT — XIAO-S3 / amp-/mik-breakout |  | MONTERAS av NextPCB (kontakt-monteringstest) — bekrafta In Stock + att THT-montering gar
J3 | 1 | PPTC141LFBN-RC | Sullins | PinSocket_1x14_P2.54mm_Vertical | Hona 1x14 2.54 THT — P4 edge A |  | MONTERAS av NextPCB (kontakt-monteringstest) — bekrafta In Stock + att THT-montering gar
J4 | 1 | PPTC151LFBN-RC | Sullins | PinSocket_1x15_P2.54mm_Vertical | Hona 1x15 2.54 THT — P4 edge |  | MONTERAS av NextPCB (kontakt-monteringstest) — bekrafta In Stock + att THT-montering gar
J5 | 1 | PPTC201LFBN-RC | Sullins | PinSocket_1x20_P2.54mm_Vertical | Hona 1x20 2.54 THT — P4-WIFI6 edge A/B (4 st/kort) |  | MONTERAS av NextPCB (kontakt-monteringstest) — bekrafta In Stock + att THT-montering gar
J6 | 1 | PREC006SAAN-RC | Sullins | PinHeader_1x06_P2.54mm_Vertical | Stift 1x6 2.54 THT — I2S MEMS-mik-breakout |  | MONTERAS av NextPCB (kontakt-monteringstest) — bekrafta In Stock + att THT-montering gar
J7 | 1 | PREC007SAAN-RC | Sullins | PinHeader_1x07_P2.54mm_Vertical | Stift 1x7 2.54 THT — MAX98357A-amp-breakout |  | MONTERAS av NextPCB (kontakt-monteringstest) — bekrafta In Stock + att THT-montering gar
J8 | 1 | B2B-PH-K-S(LF)(SN) | JST | JST_PH_B2B-PH-K_1x02_P2.00mm_Vertical | JST-PH 2p vertikal — trigger/rack/mag-switchar |  | MONTERAS av NextPCB (kontakt-monteringstest) — bekrafta In Stock + att THT-montering gar
J9 | 1 | B3B-PH-K-S(LF)(SN) | JST | JST_PH_B3B-PH-K_1x03_P2.00mm_Vertical | JST-PH 3p vertikal — recoil-styrning |  | MONTERAS av NextPCB (kontakt-monteringstest) — bekrafta In Stock + att THT-montering gar
J10 | 1 | B4B-PH-K-S(LF)(SN) | JST | JST_PH_B4B-PH-K_1x04_P2.00mm_Vertical | JST-PH 4p vertikal — NFC PN532 I2C |  | MONTERAS av NextPCB (kontakt-monteringstest) — bekrafta In Stock + att THT-montering gar
J11 | 1 | S2B-PH-K-S(LF)(SN) | JST | JST_PH_S2B-PH-K_1x02_P2.00mm_Horizontal | JST-PH 2p sido (S) — högtalare/PTT/bom-mik |  | MONTERAS av NextPCB (kontakt-monteringstest) — bekrafta In Stock + att THT-montering gar
J12 | 1 | S5B-PH-K-S(LF)(SN) | JST | JST_PH_S5B-PH-K_1x05_P2.00mm_Horizontal | JST-PH 5p sido (S) — aim-patch |  | MONTERAS av NextPCB (kontakt-monteringstest) — bekrafta In Stock + att THT-montering gar
J13 | 1 | S6B-PH-K-S(LF)(SN) | JST | JST_PH_S6B-PH-K_1x06_P2.00mm_Horizontal | JST-PH 6p sido (S) — zon/patch (10 st) |  | MONTERAS av NextPCB (kontakt-monteringstest) — bekrafta In Stock + att THT-montering gar
J14 | 1 | S2B-XH-A(LF)(SN) | JST | JST_XH_S2B-XH-A_1x02_P2.50mm_Horizontal | JST-XH 2p sido — 2S-batteri |  | MONTERAS av NextPCB (kontakt-monteringstest) — bekrafta In Stock + att THT-montering gar
J15 | 1 | SM06B-GHS-TB(LF)(SN) | JST | JST_GH_SM06B-GHS-TB_1x06-1MP_P1.25mm_Horizontal | JST-GH 6p SMD — RTK-puck (helmet J1) |  | MONTERAS av NextPCB (kontakt-monteringstest) — bekrafta In Stock + att THT-montering gar
J16 | 1 | SM08B-GHS-TB(LF)(SN) | JST | JST_GH_SM08B-GHS-TB_1x08-1MP_P1.25mm_Horizontal | JST-GH 8p SMD — ZED-F9P RTK |  | MONTERAS av NextPCB (kontakt-monteringstest) — bekrafta In Stock + att THT-montering gar
J17 | 1 | XT30PW-M | AMASS | AMASS_XT30PW-M_1x02_P2.50mm_Horizontal | XT30PW-M kraftkontakt — batteri-in |  | MONTERAS av NextPCB (kontakt-monteringstest) — bekrafta In Stock + att THT-montering gar
