robinandreeklund-collab/Strilas/hardware/led-tab-3d.step

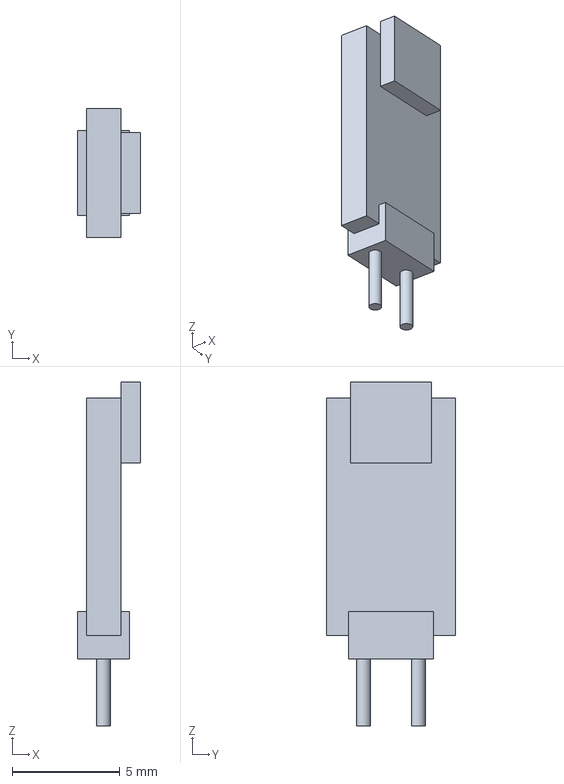
[picture p44: CAD file, 2026-06-17]
hardware/led-tab-3d.step
2.90 x 6.00 x 15.9 mm
