robinandreeklund-collab/Strilas/vapen-stack/ritningar/p4-montage-profil.png

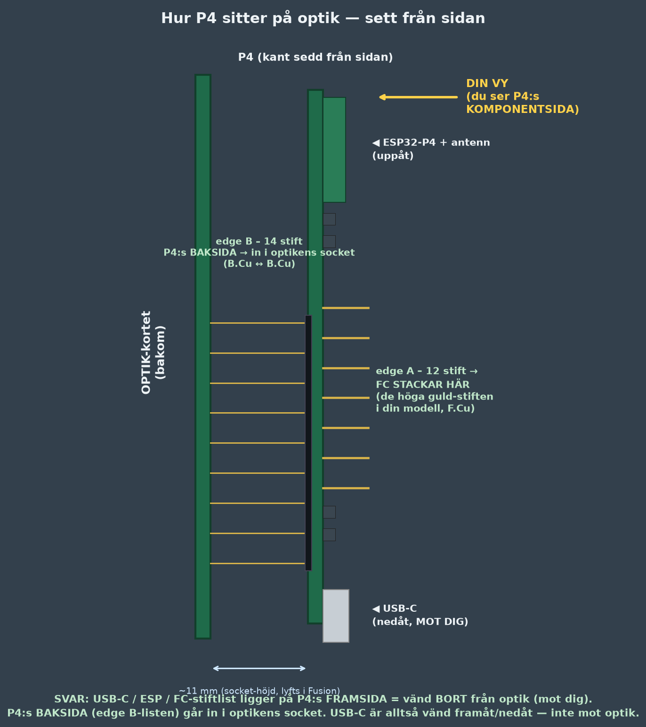
vapen-stack/ritningar/p4-montage-profil.png
