robinandreeklund-collab/Strilas/hardware/helmet-halo.kicad_pcb

## KiCad design hardware/helmet-halo.kicad_pcb (2026-06-16)

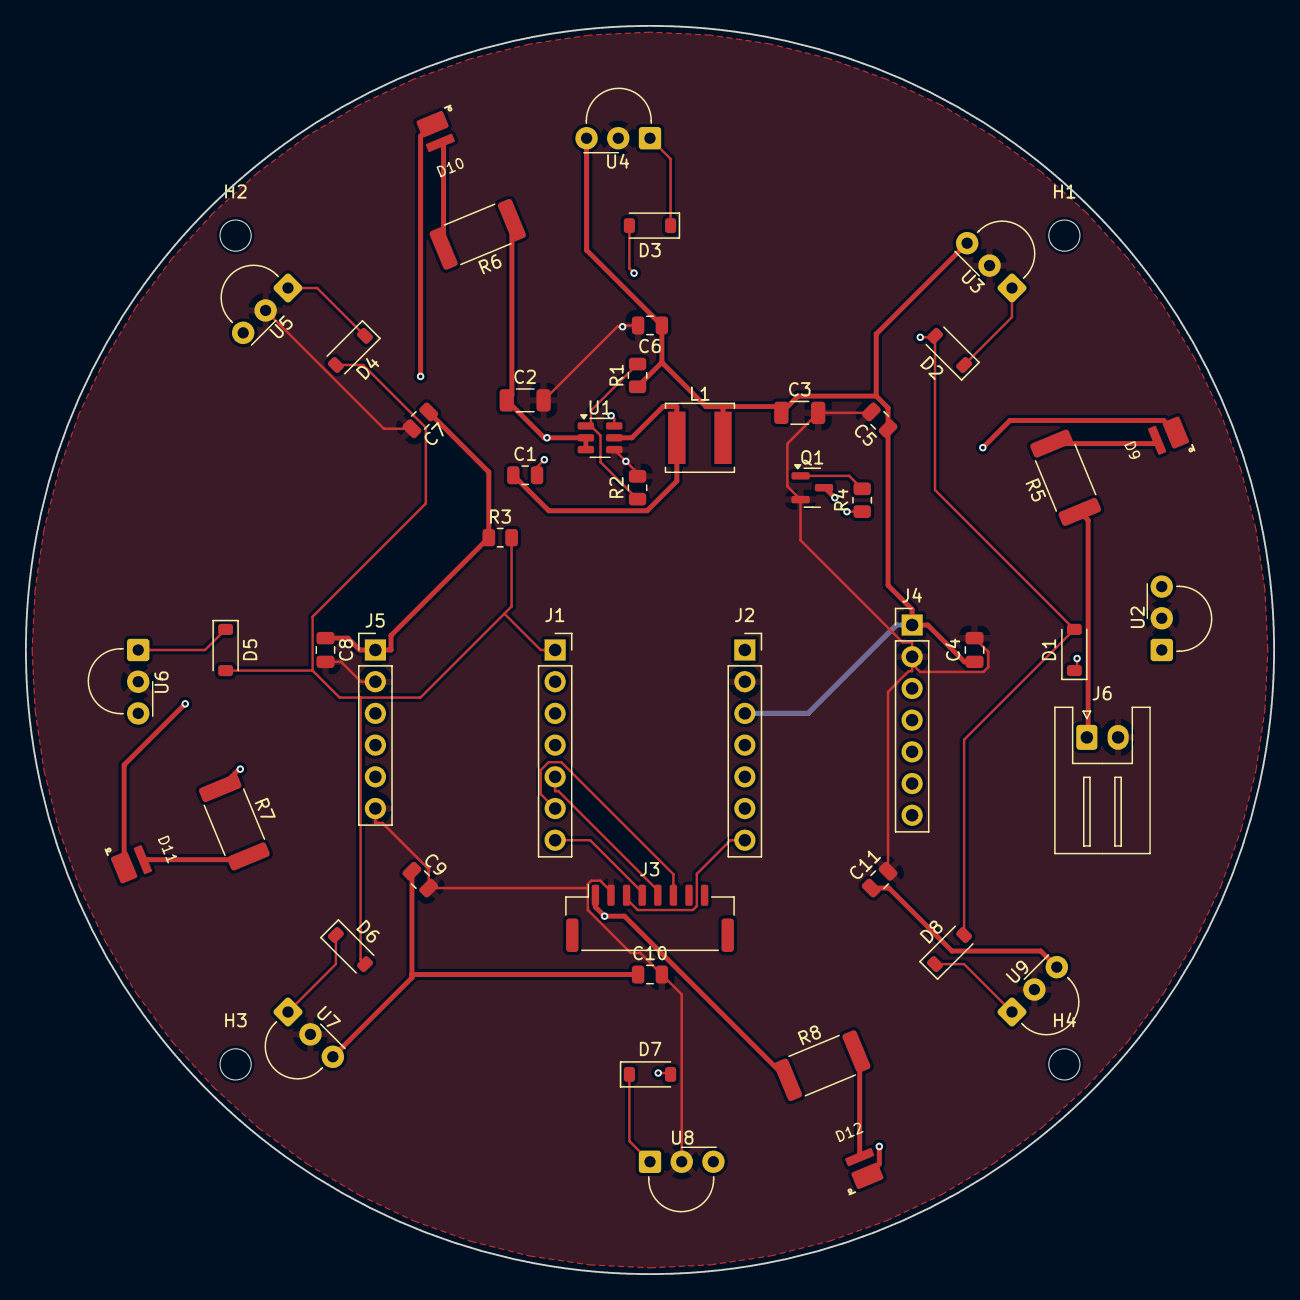
[picture p55: board helmet-halo.kicad_pcb from above]

Board: 4 copper layers, 100.0 x 100.0 mm, 52 parts (0 on the bottom side), 31 nets.

Parts:
C1, C4, C5, C6, C7, C8, C9, C10, C11: C_0805_2012Metric
C2, C3: C_1206_3216Metric
D1, D2, D3, D4, D5, D6, D7, D8: D_SOD-123
D9, D10, D11, D12: IR_Emitter_OSRAM_OSLON_Black_SFH4725S
H1, H2, H3, H4: MountingHole_2.5mm
J1, J2: PinSocket_1x07_P2.54mm_Vertical
J3: JST_GH_SM08B-GHS-TB_1x08-1MP_P1.25mm_Horizontal
J4: PinHeader_1x07_P2.54mm_Vertical
J5: PinHeader_1x06_P2.54mm_Vertical
J6: JST_XH_S2B-XH-A_1x02_P2.50mm_Horizontal
L1: L_Changjiang_FNR5040S
Q1: SOT-23
R1, R2, R3, R4: R_0805_2012Metric
R5, R6, R7, R8: R_2512_6332Metric
U1: TSOT-23-6
U2, U3, U4, U5, U6, U7, U8, U9: Vishay_MINIMOLD-3Pin

Connections:
+3V3: C3.1, C4.1, C5.1, C6.1, C7.1, C8.1, C9.1, C10.1, C11.1, J2.3, J4.1, J5.1, L1.2, R1.1, R3.1, U2.3, U3.3, U4.3, U5.3, U6.3, U7.3, U8.3, U9.3
AMP_SD: J2.4, J4.3
BST: C1.2, U1.6
DATA: D1.2, D2.2, D3.2, D4.2, D5.2, D6.2, D7.2, D8.2, J1.1, R3.2
FB: R1.2, R2.1, U1.1
GND: C2.2, C3.2, C4.2, C5.2, C6.2, C7.2, C8.2, C9.2, C10.2, C11.2, J2.2, J3.2, J4.2, J5.2, J5.6, J6.2, Q1.2, R2.2, U1.4, U2.2, U3.2, U4.2, U5.2, U6.2, U7.2, U8.2, U9.2
GNSS_RX: J1.7, J3.4
GNSS_TX: J2.7, J3.3
I2C_SCL: J1.6, J3.6
I2C_SDA: J1.5, J3.5
I2S_BCLK: J1.3, J4.6, J5.5
I2S_DIN: J2.5, J5.3
I2S_DOUT: J2.6, J4.5
I2S_LRCK: J1.4, J4.7, J5.4
LED_A1: D9.1, R5.2
LED_A2: D10.1, R6.2
LED_A3: D11.1, R7.2
LED_A4: D12.1, R8.2
LED_CATH: D9.2, D10.2, D11.2, D12.2, Q1.3
LED_EN: J1.2, R4.1
unnamed: Q1.1, R4.2
OUT1: D1.1, U2.1
OUT2: D2.1, U3.1
OUT3: D3.1, U4.1
OUT4: D4.1, U5.1
OUT5: D5.1, U6.1
OUT6: D6.1, U7.1
OUT7: D7.1, U8.1
OUT8: D8.1, U9.1
SW: C1.1, L1.1, U1.5
VBAT: C2.1, J3.1, J6.1, R5.1, R6.1, R7.1, R8.1, U1.2, U1.3
