robinandreeklund-collab/Strilas/vapen-stack/weapon-module.kicad_pcb

## KiCad design vapen-stack/weapon-module.kicad_pcb (2026-06-16)

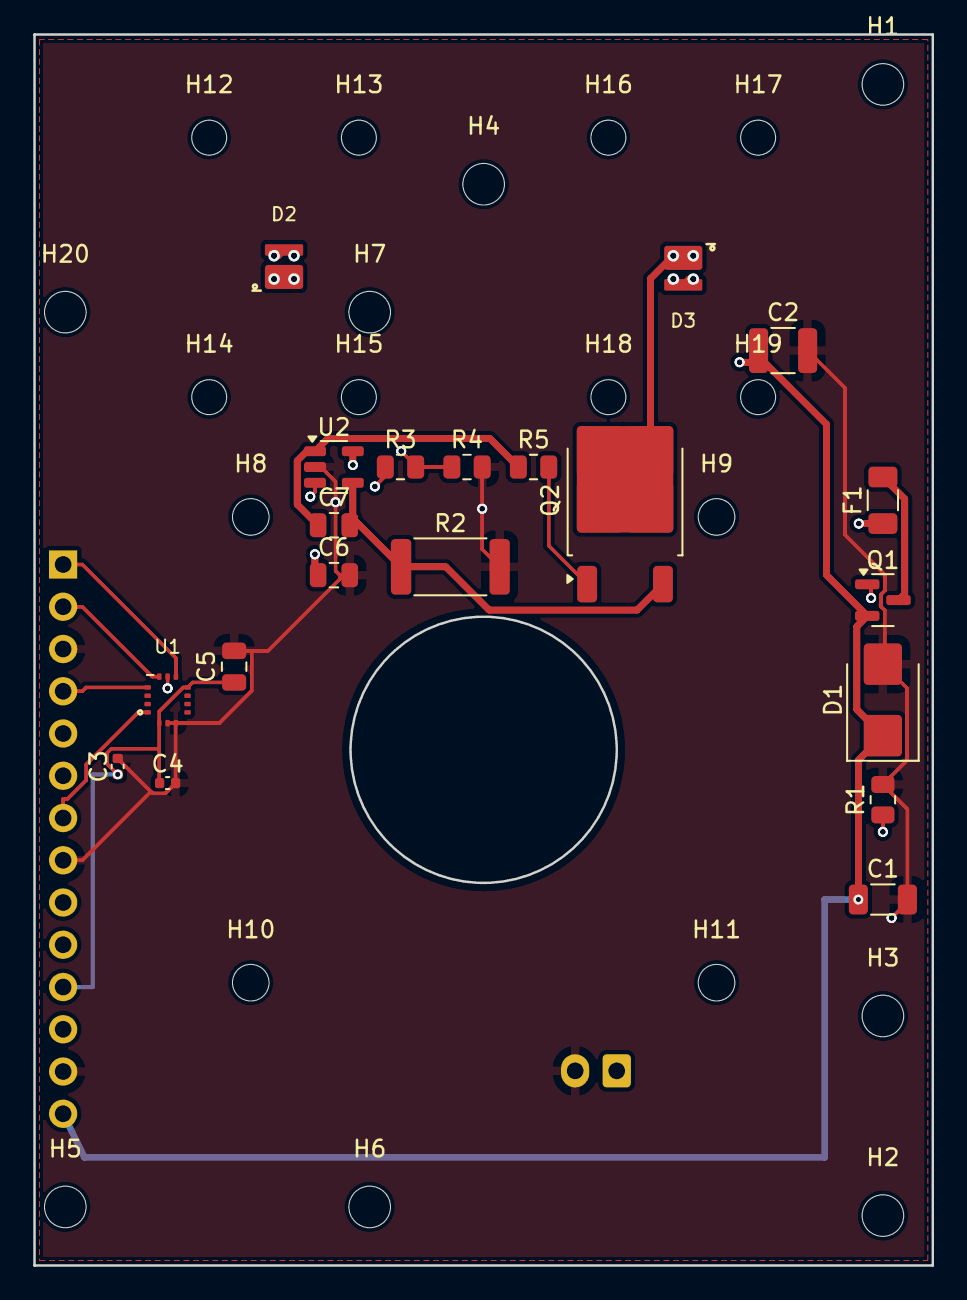
[picture p56: board vapen-stack/weapon-module.kicad_pcb from above]

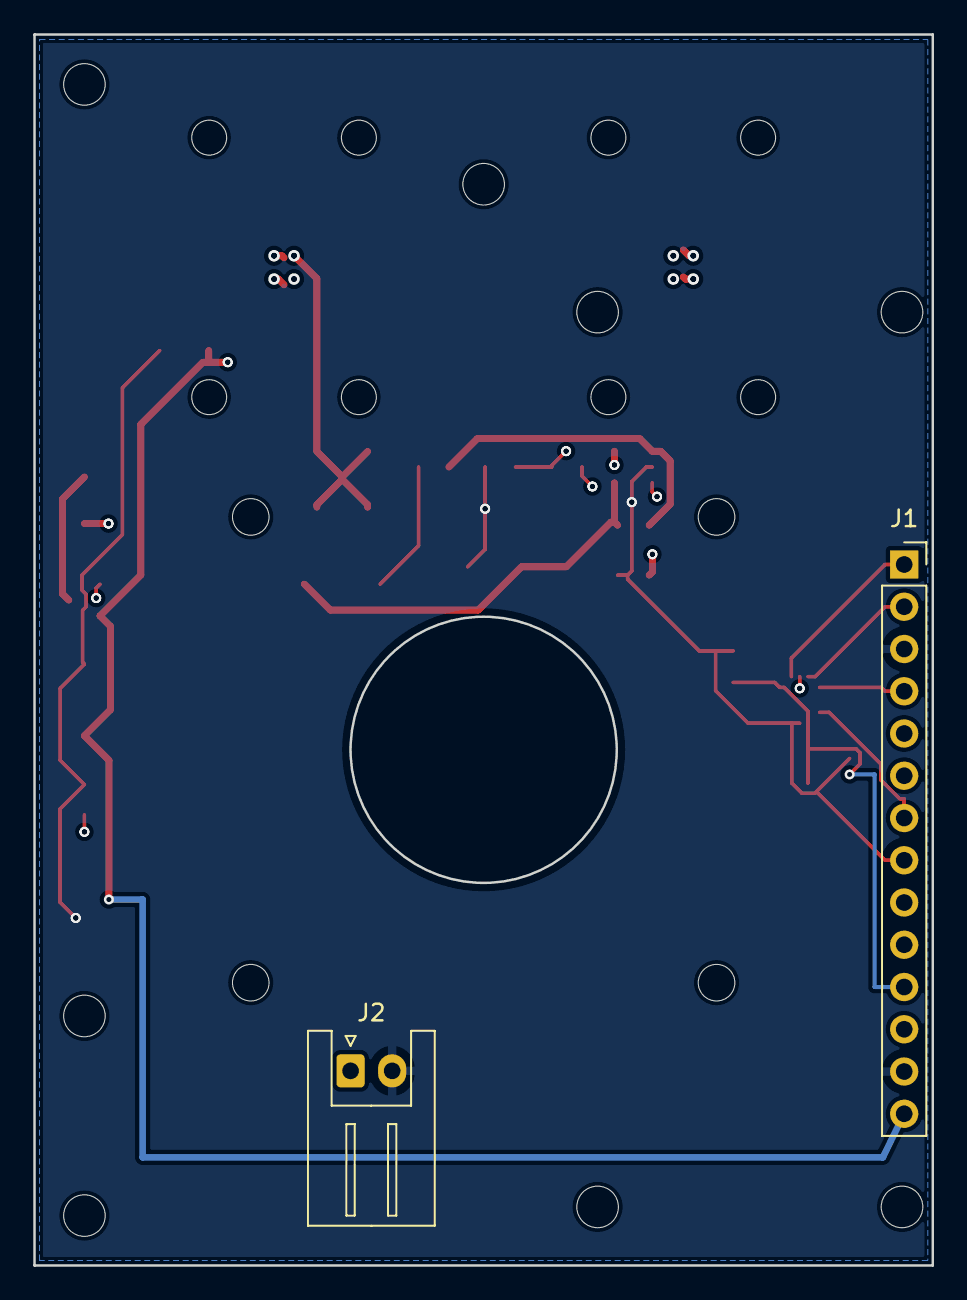
[picture p57: board vapen-stack/weapon-module.kicad_pcb from below]

Board: 4 copper layers, 54.0 x 74.0 mm, 42 parts (2 on the bottom side), 18 nets.

Parts:
C1: C_1206_3216Metric
C2: C_1210_3225Metric
C3, C4: C_0402_1005Metric
C5, C6, C7: C_0805_2012Metric
D1: D_SMB
D2, D3: IR_Emitter_OSRAM_OSLON_Black_SFH4725S
F1: Fuse_1206_3216Metric
H1, H2, H3, H4, H5, H6, H7, H20: MountingHole_2.5mm
H8, H9, H10, H11: MountingHole_2.2mm_M2
H12, H13, H14, H15, H16, H17, H18, H19: MountingHole_2.1mm
J1: PinSocket_1x14_P2.54mm_Vertical
J2: JST_XH_S2B-XH-A_1x02_P2.50mm_Horizontal
Q1: SOT-23
Q2: TO-252-2
R1, R3, R4, R5: R_0805_2012Metric
R2: R_2512_6332Metric
U1: InvenSense_LGA-14_2.5x3mm_ICM-456xx
U2: SOT-23-5

Connections:
+3V3: C3.1, C4.1, C5.1, J1.11, U1.5, U1.8
DRV_GATE: Q2.1, R5.2
GND: C1.2, C2.2, C3.2, C4.2, C5.2, C6.2, D1.2, J1.3, J1.8, J1.13, J2.2, R1.2, R2.2, R4.2, U1.6, U1.7, U2.2
IDRV_REF: R3.2, R4.1, U2.3
IDRV_SENSE: C7.2, Q2.3, R2.1, U2.4
IMU_INT: J1.4, U1.4
IR_MOD: J1.10, R3.1
LED_CATH: D3.2, Q2.2
LED_MID: D2.2, D3.1
MISO: J1.7, U1.1
MOSI: J1.2, U1.14
unnamed: Q1.1, R1.1
unnamed: C7.1, R5.1, U2.1
SCK: J1.6, U1.13
VBAT: C1.1, C2.1, C6.1, D1.1, D2.1, J1.14, Q1.2, U2.5
VBAT_F: F1.2, Q1.3
VBAT_IN: F1.1, J2.1
nCS: J1.1, U1.12
