robinandreeklund-collab/Strilas/hardware/route_vest.py

#!/usr/bin/env python3
"""STRILAS — route väst-patch (2-lager): freeroute ALLA nät (inkl GND som spår → inga
GND-öar), applicera SES, verifiera (0 oroutade + 0 oconnected + 0 clearance), Gerbers/STEP.
(pour_gnd finns kvar men används ej i no-pour-flödet.)"""
import subprocess, sys, math, shutil, pcbnew
PCB="hardware/vest-patch.kicad_pcb"; DSN="hardware/vest-patch.dsn"; SES="hardware/vest-patch.ses"
MM=pcbnew.FromMM

def _typed_load(path, tries=40):
    """pcbnew-SWIG ger ibland otypat board → ladda om tills Footprints/Tracks/Zones funkar."""
    for _ in range(tries):
        b = pcbnew.LoadBoard(path)
        try:
            list(b.GetFootprints()); list(b.GetTracks()); list(b.Zones()); return b
        except TypeError:
            continue
    raise RuntimeError("kunde ej få typat board")

def gnd_code(b):
    for f in b.GetFootprints():
        for pd in f.Pads():
            if pd.GetNetname()=="GND": return pd.GetNetCode()
    return None

def pour_gnd(path, stitch=True):
    b=_typed_load(path)
    for z in [x for x in b.Zones()]: b.Remove(z)
    bb=b.GetBoardEdgesBoundingBox(); gnd=gnd_code(b); m=MM(0.4)
    for layer in (pcbnew.F_Cu, pcbnew.B_Cu):
        z=pcbnew.ZONE(b); z.SetLayer(layer); z.SetNetCode(gnd)
        z.SetLocalClearance(MM(0.25)); z.SetMinThickness(MM(0.2)); z.SetIsFilled(False)
        z.SetPadConnection(pcbnew.ZONE_CONNECTION_FULL)
        ch=pcbnew.SHAPE_LINE_CHAIN()
        for x,y in [(bb.GetLeft()+m,bb.GetTop()+m),(bb.GetRight()-m,bb.GetTop()+m),
                    (bb.GetRight()-m,bb.GetBottom()-m),(bb.GetLeft()+m,bb.GetBottom()-m)]:
            ch.Append(int(x),int(y))
        ch.SetClosed(True); z.AddPolygon(ch); b.Add(z)
    if stitch:   # GND-stitchning F↔B vid fria mitt-kanter (klart av komponenter; origo 150,120)
        for dx,dy in [(-26,8),(26,8),(-26,-12),(26,-12)]:
            v=pcbnew.PCB_VIA(b); v.SetPosition(pcbnew.VECTOR2I(MM(150+dx),MM(120-dy)))
            v.SetDrill(MM(0.4)); v.SetWidth(MM(0.8)); v.SetNetCode(gnd); b.Add(v)
    pcbnew.ZONE_FILLER(b).Fill(b.Zones()); pcbnew.SaveBoard(path,b)

def unrouted(path):
    b=_typed_load(path); tr={}
    for t in b.GetTracks(): tr.setdefault(t.GetNetCode(),[]).extend(
        [(t.GetStart().x/1e6,t.GetStart().y/1e6),(t.GetEnd().x/1e6,t.GetEnd().y/1e6)])
    return sum(1 for f in b.GetFootprints() for p in f.Pads() if p.GetNetname() not in ("","GND")
        and not any(math.hypot(p.GetPosition().x/1e6-ex,p.GetPosition().y/1e6-ey)<0.4 for ex,ey in tr.get(p.GetNetCode(),[])))

def verify(path):
    b=_typed_load(path); CU=[pcbnew.F_Cu,pcbnew.B_Cu]; items=[]
    for t in b.GetTracks():
        lays=CU if t.Type()==pcbnew.PCB_VIA_T else [t.GetLayer()]
        items.append((t.GetNetCode(),set(lays),t.GetEffectiveShape()))
    for f in b.GetFootprints():
        for pd in f.Pads(): items.append((pd.GetNetCode(),set(L for L in CU if pd.IsOnLayer(L)),pd.GetEffectiveShape()))
    v=sum(1 for i in range(len(items)) for j in range(i+1,len(items))
          if items[i][0]!=items[j][0] and (items[i][1]&items[j][1]) and items[i][2].Collide(items[j][2],int(0.2e6)))
    b.BuildConnectivity()
    try: un=b.GetConnectivity().GetUnconnectedCount(True)
    except TypeError: un=b.GetConnectivity().GetUnconnectedCount()
    return v,un

# 1) route ALLA nät (inkl GND som spår) — freerouting kopplar varje GND-nod → inga öar
b=_typed_load(PCB)
for t in list(b.GetTracks()): b.Remove(t)        # rensa ev. spår/via från tidigare routning
for z in list(b.Zones()): b.Remove(z)            # ren DSN (inga "multiple vias skipped" → ingen modal-dialog-hängning)
pcbnew.SaveBoard(PCB,b)
shutil.copy(PCB,"/tmp/_vest_pp.kicad_pcb")
pcbnew.ExportSpecctraDSN(b,DSN)
# bredda kraft-/LED-nät till 0,4 mm (TSOP-3V3 stannar smalt; LED-grenar bär ~0,5 A)
subprocess.run(["python3","hardware/dsn_power_class.py",DSN])
clean=False
for seed in range(1,13):
    subprocess.run(["xvfb-run","-a","java","-jar","/opt/freerouting.jar","-de",DSN,"-do",SES,"-mp","200"],
                   stdout=subprocess.DEVNULL,stderr=subprocess.DEVNULL)
    shutil.copy("/tmp/_vest_pp.kicad_pcb",PCB)
    subprocess.run(["python3","hardware/ses_apply.py",PCB,SES],stdout=subprocess.DEVNULL)
    u=unrouted(PCB)
    if u>0: print(f"  seed {seed}: signal-oroutade={u}"); continue
    v,un=verify(PCB)
    print(f"  seed {seed}: signal-oroutade=0  clearance={v}  oconnected={un}")
    if v==0 and un==0: clean=True; break   # signal + GND (no-pour-spår) alla rena
if not clean: print("!! ingen helt ren routning"); sys.exit(1)
print("REN board.")
import os
os.system("rm -rf /tmp/gbv && mkdir -p /tmp/gbv")
subprocess.run(["kicad-cli","pcb","export","gerbers","-o","/tmp/gbv/",PCB],stdout=subprocess.DEVNULL,stderr=subprocess.DEVNULL)
subprocess.run(["kicad-cli","pcb","export","drill","-o","/tmp/gbv/",PCB],stdout=subprocess.DEVNULL,stderr=subprocess.DEVNULL)
subprocess.run(["bash","-c","cd /tmp/gbv && zip -q -r - . > /home/user/Strilas/hardware/vest-patch-gerbers.zip"])
subprocess.run(["kicad-cli","pcb","export","step","-f","--subst-models","-o","hardware/vest-patch.step",PCB],stdout=subprocess.DEVNULL,stderr=subprocess.DEVNULL)
print("Gerbers + STEP exporterade.")
