robinandreeklund-collab/Strilas/firmware/target_node.py

"""STRILAS firmware-skelett — MÅL-NOD (väst/hjälm, ESP32-C5-logik).
TSOP avkodar strålen → IRHit. Sänder även låg-rate PlayerState (position/fart) för
serverns lag-komp-rewind. HW-abstraherad: on_ir()/state() matas av sensorer (sim/HW)."""
from .protocol import IRHit, PlayerState


class TargetNode:
    def __init__(self, target_id=1):
        self.id = target_id
        self.seq = 0
        self.x = self.y = self.z = 0.0
        self.vx = self.vy = 0.0

    def on_ir(self, ir_code, shooter_id, t, zone_hint="Bröst", rssi=-40.0):
        self.seq += 1
        return IRHit(target_id=self.id, t_rx=t, ir_code=ir_code,
                     shooter_id_decoded=shooter_id, zone_hint=zone_hint,
                     rssi=rssi, seq=self.seq)

    def state(self, t):
        return PlayerState(self.id, t, self.x, self.y, self.z, self.vx, self.vy)
